jgraichen/railway-signals/kicad/Hauptsignal/README.md

# Hauptsignal HSv1

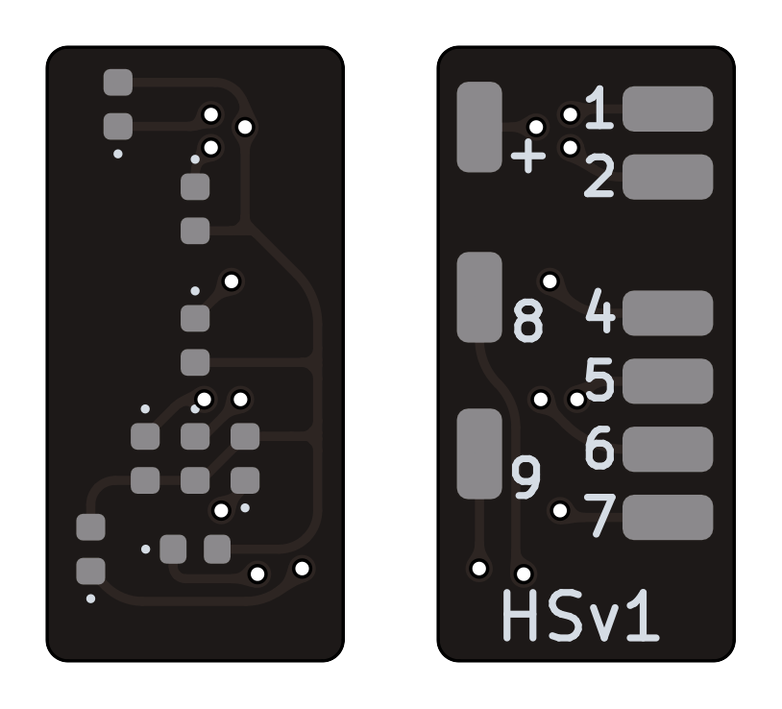
[picture p16: kicad/Hauptsignal/Hauptsignal.png]


Geeignet für KS-Hauptsignale.

## Anschlussbelegung

| Schema | Pin-Belegung |
| --- | --- |
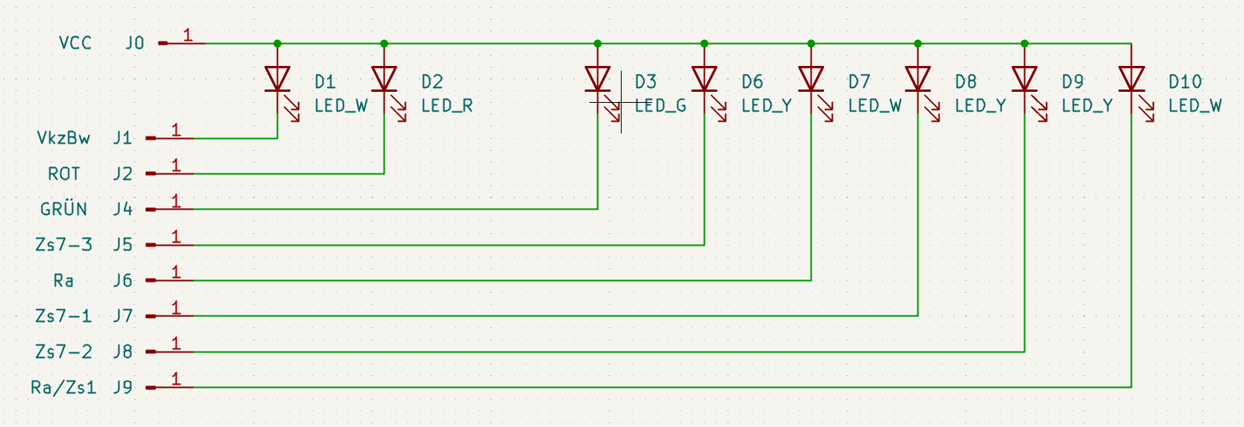
[picture p17: kicad/Hauptsignal/schema.png]
Schema
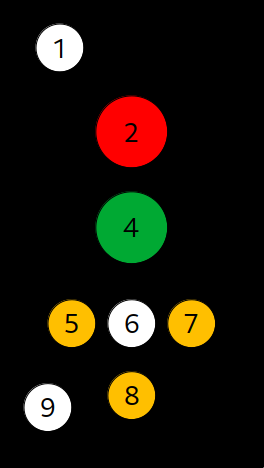
[picture p18: kicad/Hauptsignal/schema_vis.png]
Pin-Belegung
|  |  |

| Referenz | Pin | LED | Funktion |
| --- | --- | --- | --- |
| J0 | + | | Stromversorgung (+) |
| J1 | 1 | Kaltweiß | Zusatzlicht (oben) |
| J2 | 2 | Rot | Hp0 (Halt) |
| J4 | 4 | Grün | Ks1 (Fahrt) |
| J5 | 5 | Gelb | Zs7 |
| J6 | 6 | Kaltweiß | Sh1/Ra12 |
| J7 | 7 | Gelb | Zs7 |
| J8 | 8 | Gelb | Zs7 |
| J9 | 9 | Kaltweiß | Sh1/Ra12/Zs1/Zusatzlicht (unten) |

## License

This work is licensed under a
[Creative Commons Attribution-ShareAlike 4.0 International License](http://creativecommons.org/licenses/by-sa/4.0/).

(http://creativecommons.org/licenses/by-sa/4.0/)
