jgraichen/railway-signals/freecad/KS/Example/export/MS_48_80_1-front.png

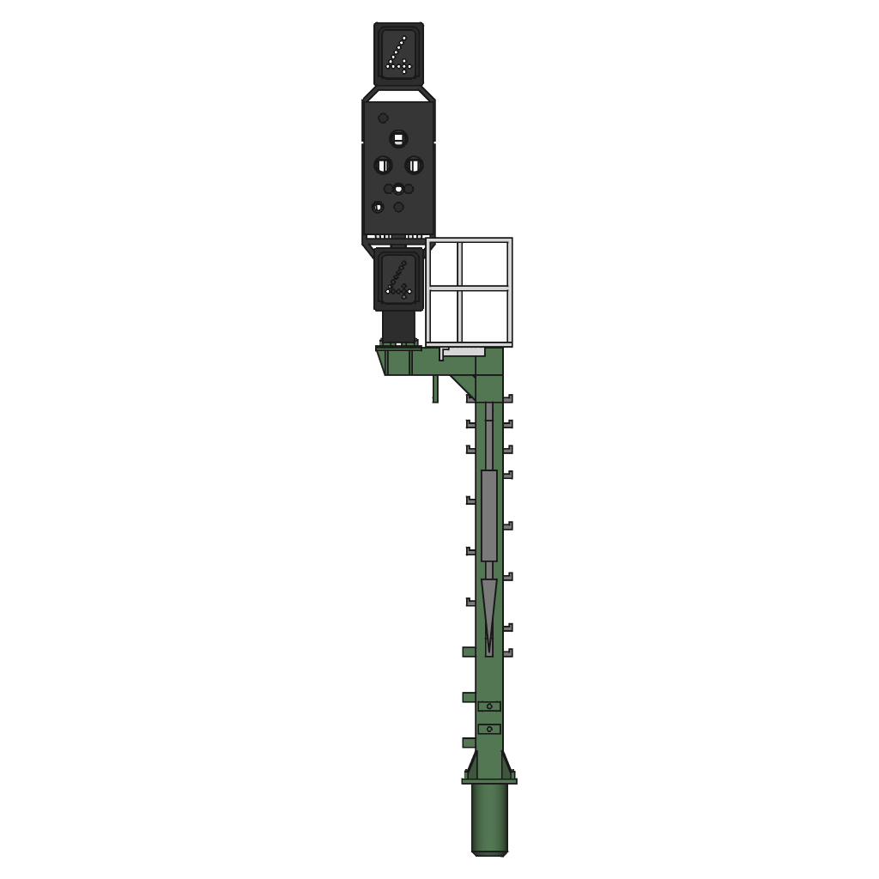
freecad/KS/Example/export/MS_48_80_1-front.png
