jgraichen/railway-signals/freecad/KS/Signalschirme/export/MS__B-axo.png

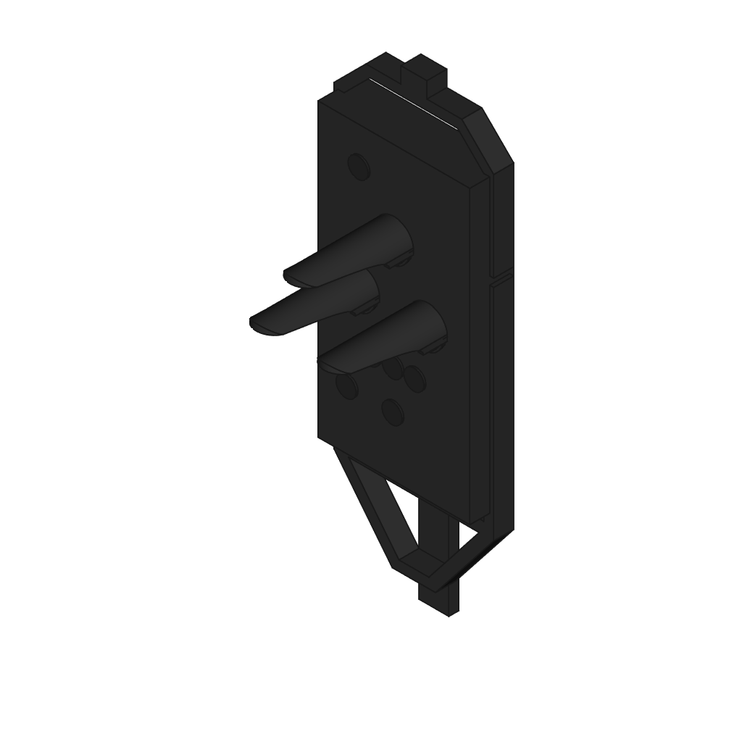
freecad/KS/Signalschirme/export/MS__B-axo.png
