jgraichen/railway-signals/freecad/KS/Zusatzsignale/export/ZS_Zs2_P-axo.png

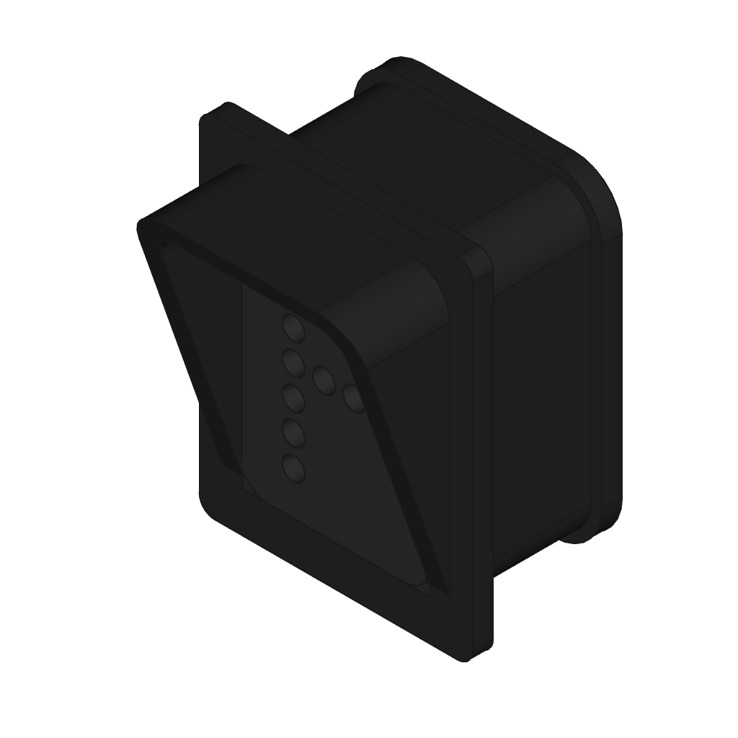
freecad/KS/Zusatzsignale/export/ZS_Zs2_P-axo.png
