jgraichen/railway-signals/freecad/KS/Zusatzsignale/export/ZS_Zs6_NR-axo.png

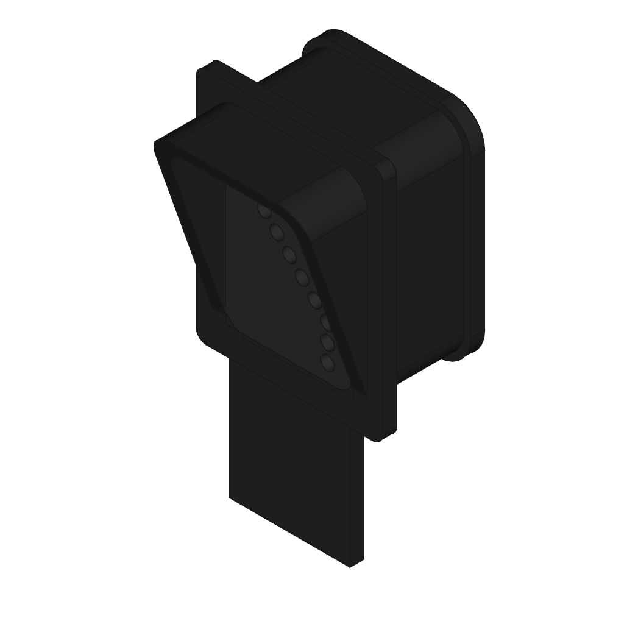
freecad/KS/Zusatzsignale/export/ZS_Zs6_NR-axo.png
