jgraichen/railway-signals/freecad/watti-signal-mount/png/watti-plate-axo.png

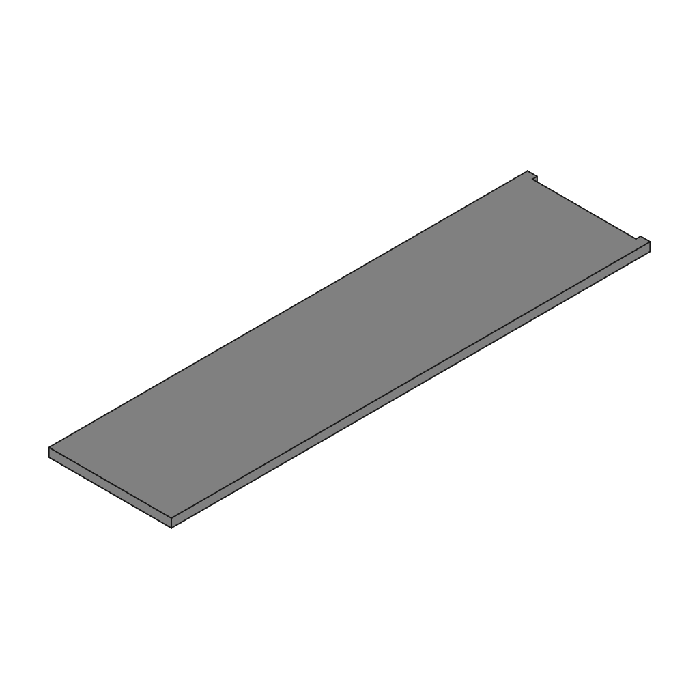
freecad/watti-signal-mount/png/watti-plate-axo.png
