jgraichen/railway-signals/freecad/KS/Signalschirme/export/MS_Zs7_Sh1_vBw__B.step

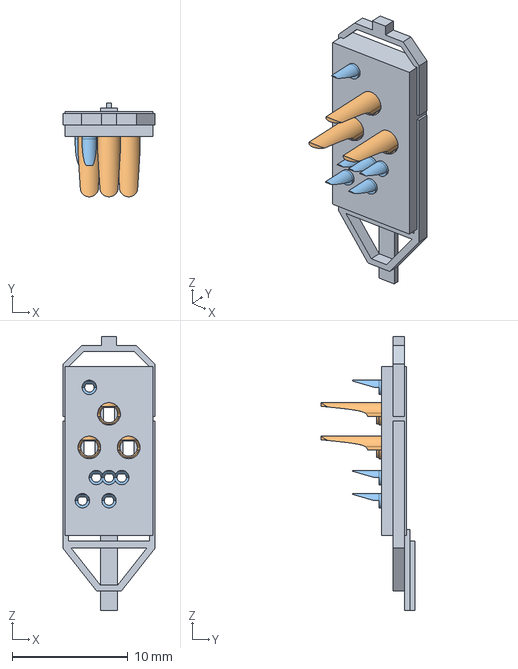
[picture p129: CAD file, 2026-01-25]
freecad/KS/Signalschirme/export/MS_Zs7_Sh1_vBw__B.step
8.00 x 8.10 x 23.7 mm
