jgraichen/railway-signals/freecad/KS/Signalschirme/parts/HS_Schute_15.FCStd

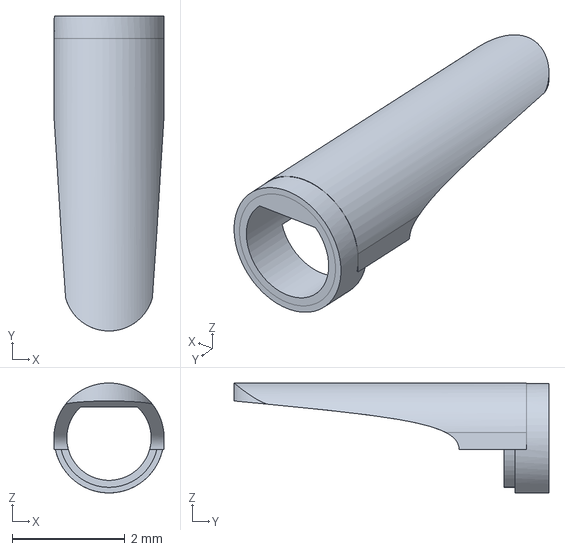
[picture p130: CAD file, 2026-01-25]
freecad/KS/Signalschirme/parts/HS_Schute_15.FCStd
1.95 x 5.60 x 1.96 mm
