jgraichen/railway-signals/freecad/KS/Zusatzsignale/export/ZS_Zs3_3.step

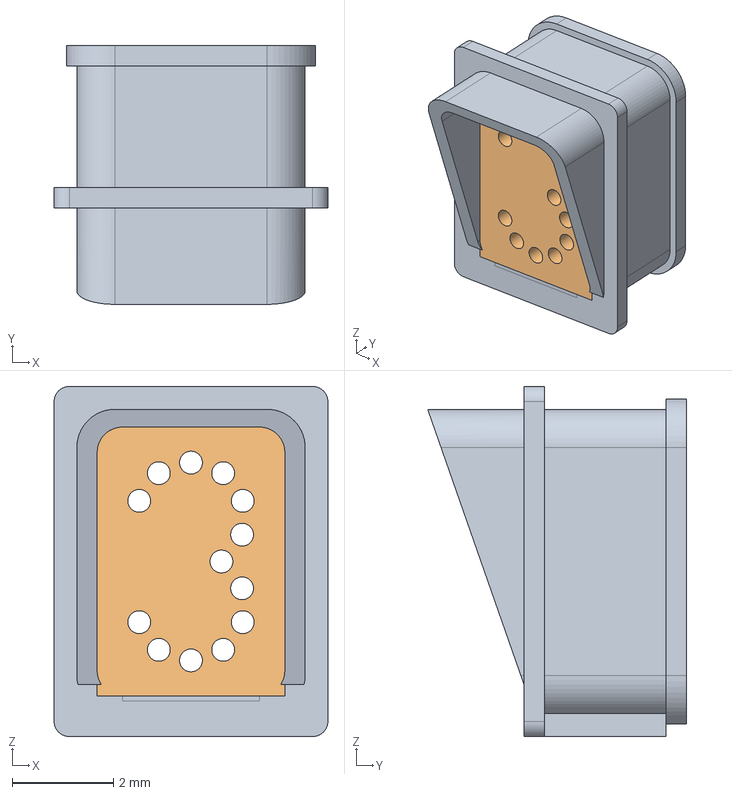
[picture p131: CAD file, 2026-01-25]
freecad/KS/Zusatzsignale/export/ZS_Zs3_3.step
5.40 x 5.10 x 6.90 mm
