jgraichen/railway-signals/freecad/watti-signal-mount/export/watti-plate.step

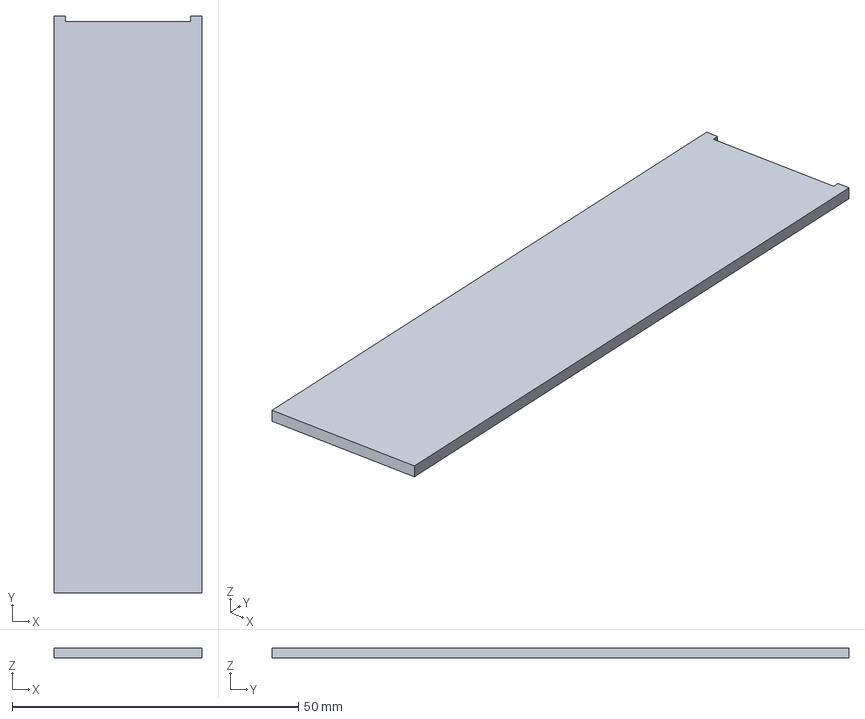
[picture p132: CAD file, 2024-03-24]
freecad/watti-signal-mount/export/watti-plate.step
25.8 x 100.8 x 1.80 mm
