jgraichen/railway-signals/freecad/watti-signal-mount/parts/M3-mount.FCStd

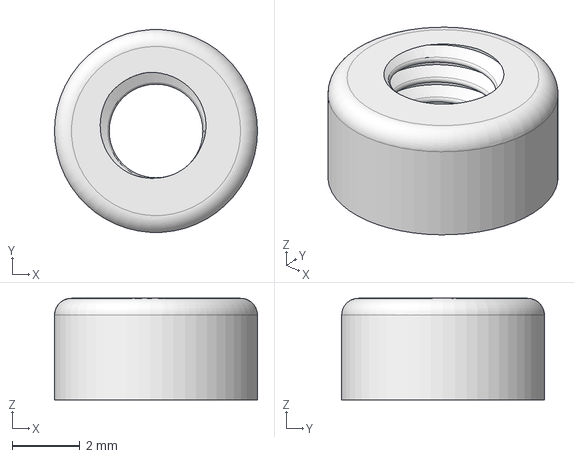
[picture p133: CAD file, 2023-12-09]
freecad/watti-signal-mount/parts/M3-mount.FCStd
6.00 x 5.99 x 3.00 mm
