jgraichen/railway-signals/freecad/KS/Masten/export/Auslegermast_48_40L_1ZS.step

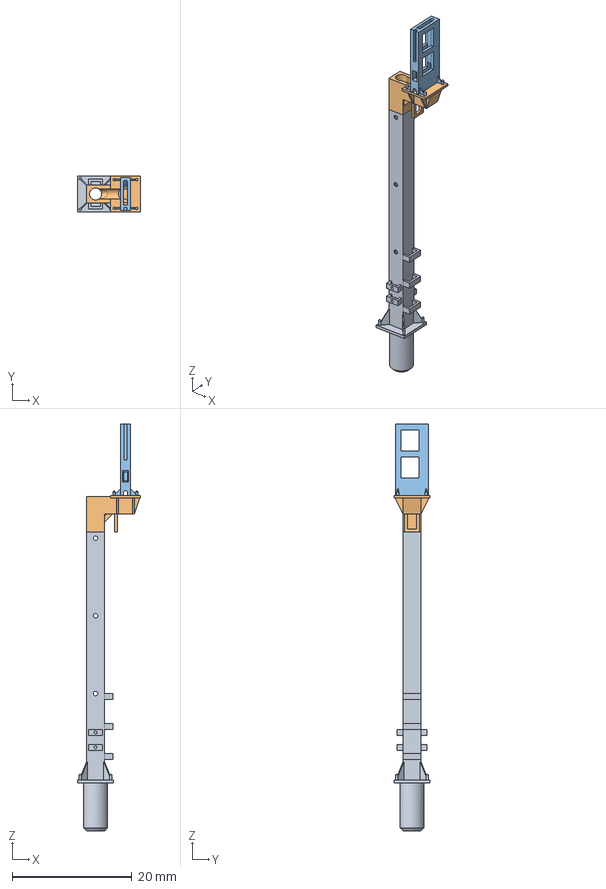
[picture p134: CAD file, 2024-05-25]
freecad/KS/Masten/export/Auslegermast_48_40L_1ZS.step
10.5 x 6.00 x 68.1 mm
Mast_42
Ausleger_40
Signalmast_1ZS
