jgraichen/railway-signals/freecad/KS/Masten/parts/Part_Mast_42.FCStd

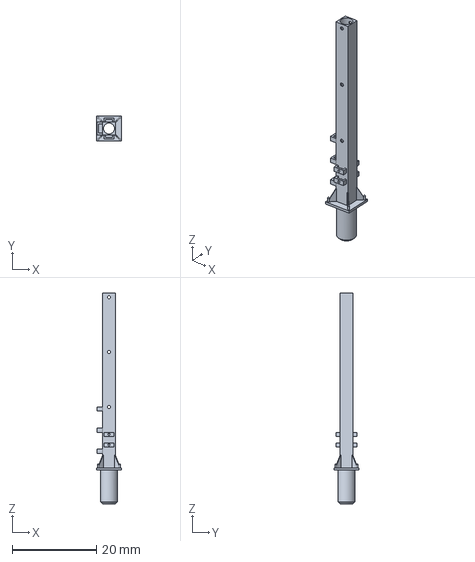
[picture p135: CAD file, 2024-06-06]
freecad/KS/Masten/parts/Part_Mast_42.FCStd
6.00 x 6.00 x 50.0 mm
