jgraichen/railway-signals/freecad/KS/Signalschirme/parts/MS_Schirm_mit_Zs.FCStd

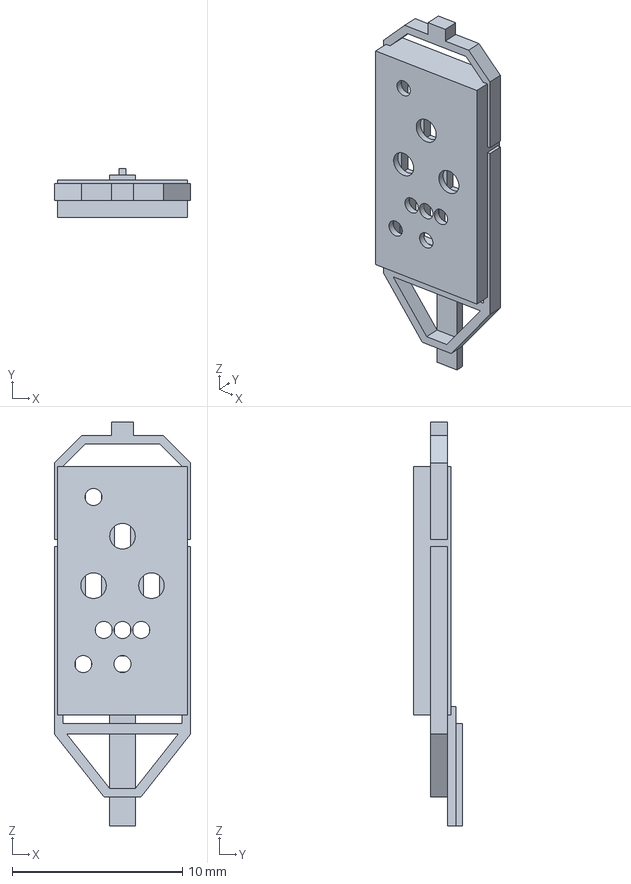
[picture p137: CAD file, 2026-01-25]
freecad/KS/Signalschirme/parts/MS_Schirm_mit_Zs.FCStd
8.00 x 2.90 x 23.7 mm
