jgraichen/railway-signals/freecad/KS/Zusatzsignale/parts/ZS_Nummer.FCStd

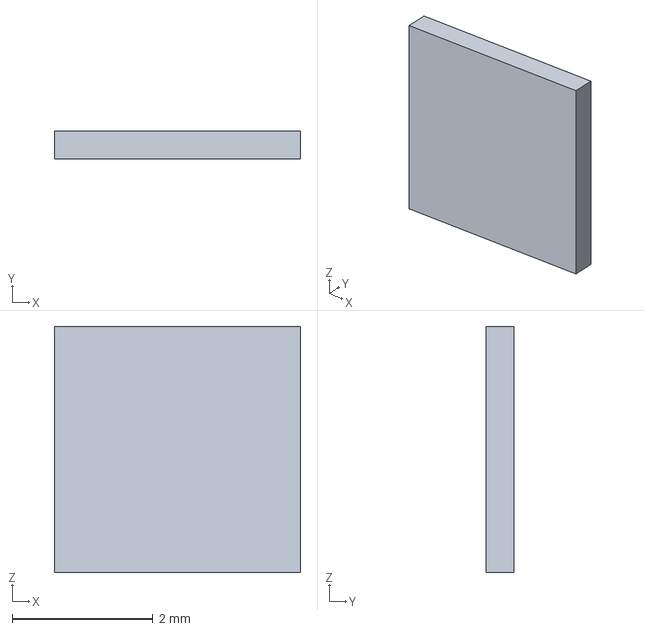
[picture p138: CAD file, 2026-01-25]
freecad/KS/Zusatzsignale/parts/ZS_Nummer.FCStd
3.50 x 0.4 x 3.50 mm
