jgraichen/railway-signals/freecad/KS/Masten/export/Leiter_16.step

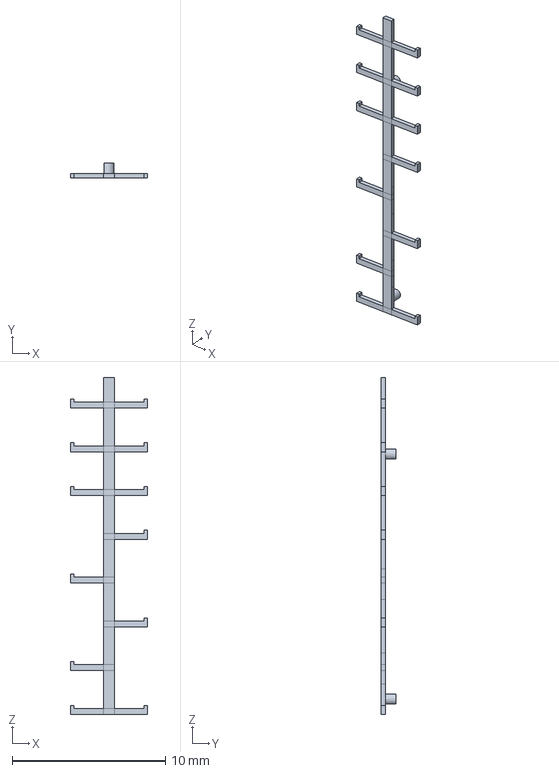
[picture p139: CAD file, 2024-05-24]
freecad/KS/Masten/export/Leiter_16.step
5.00 x 1.00 x 22.0 mm
