jgraichen/railway-signals/freecad/KS/Masten/parts/Part_Mast_52.FCStd

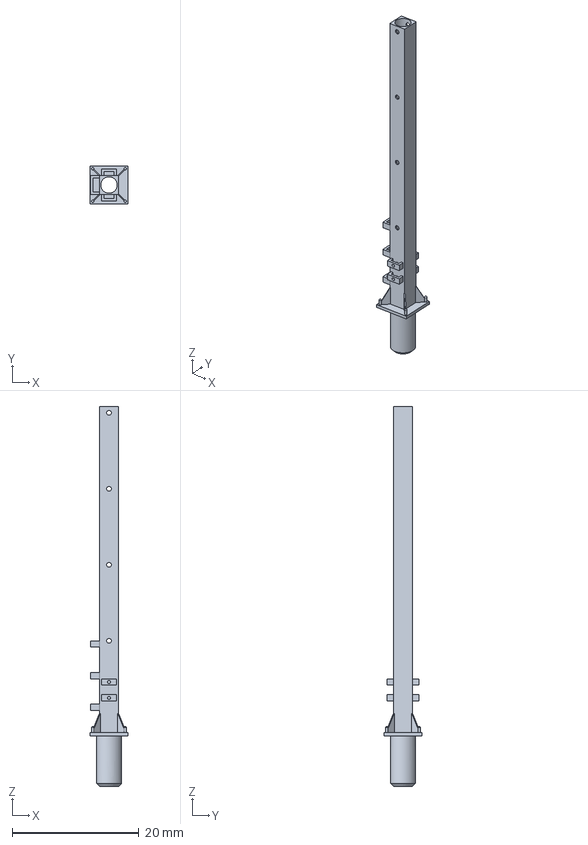
[picture p140: CAD file, 2024-05-24]
freecad/KS/Masten/parts/Part_Mast_52.FCStd
6.00 x 6.00 x 60.0 mm
