jgraichen/railway-signals/freecad/KS/Signalschirme/parts/HS_Schirm_Blindstopfen_10.FCStd

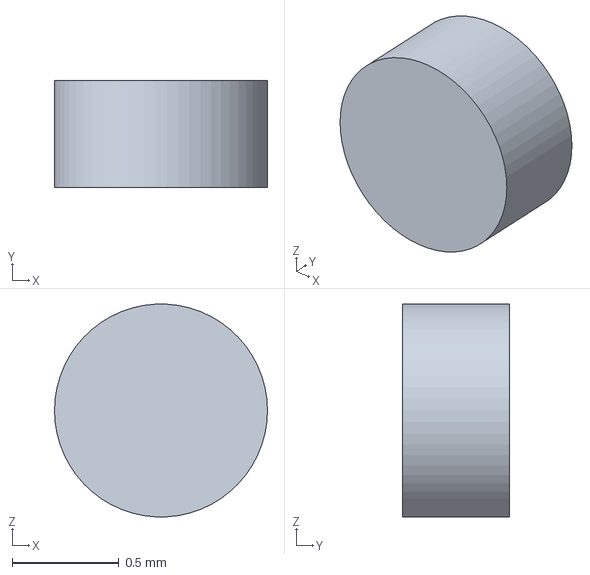
[picture p142: CAD file, 2026-01-25]
freecad/KS/Signalschirme/parts/HS_Schirm_Blindstopfen_10.FCStd
1.00 x 0.5 x 0.999 mm
