jgraichen/railway-signals/freecad/KS/Zusatzsignale/parts/ZS_Tafel_2.FCStd

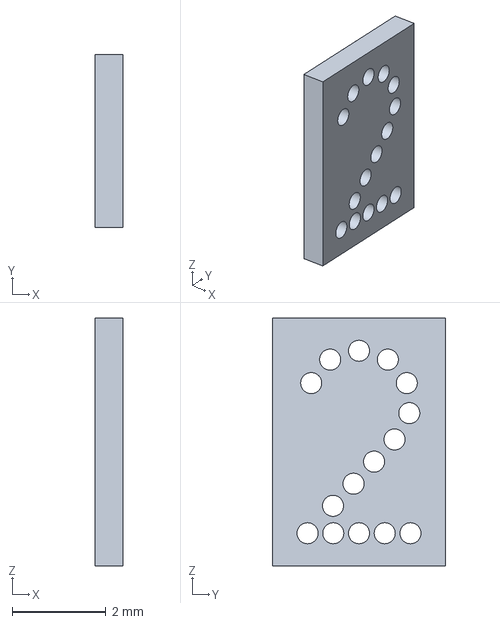
[picture p143: CAD file, 2026-01-25]
freecad/KS/Zusatzsignale/parts/ZS_Tafel_2.FCStd
0.6 x 3.70 x 5.30 mm
