jgraichen/railway-signals/freecad/KS/Masten/export/Auslegermast_48_40R_1ZS.step

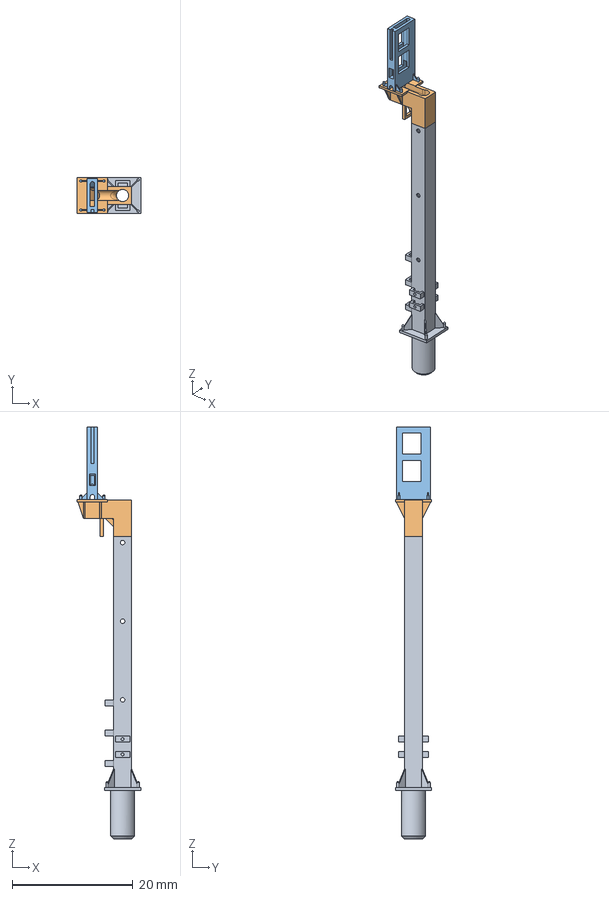
[picture p144: CAD file, 2024-05-24]
freecad/KS/Masten/export/Auslegermast_48_40R_1ZS.step
10.5 x 6.00 x 68.1 mm
Mast_42
Ausleger_40
Signalmast_1ZS
