jgraichen/railway-signals/freecad/KS/Masten/parts/Part_Ausleger_80.FCStd

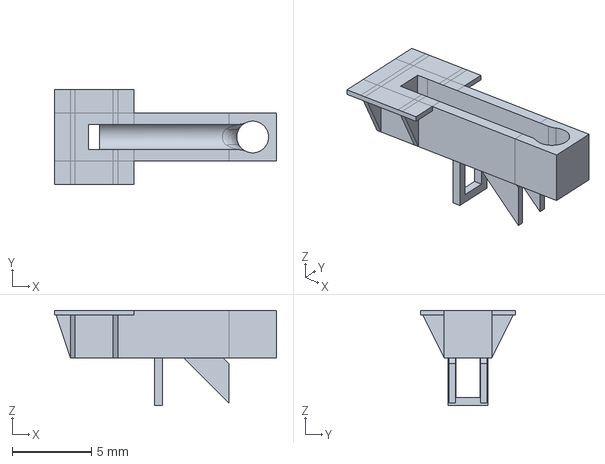
[picture p145: CAD file, 2024-05-24]
freecad/KS/Masten/parts/Part_Ausleger_80.FCStd
14.0 x 6.00 x 6.00 mm
