jgraichen/railway-signals/freecad/KS/Signalschirme/export/VS_Wd.step

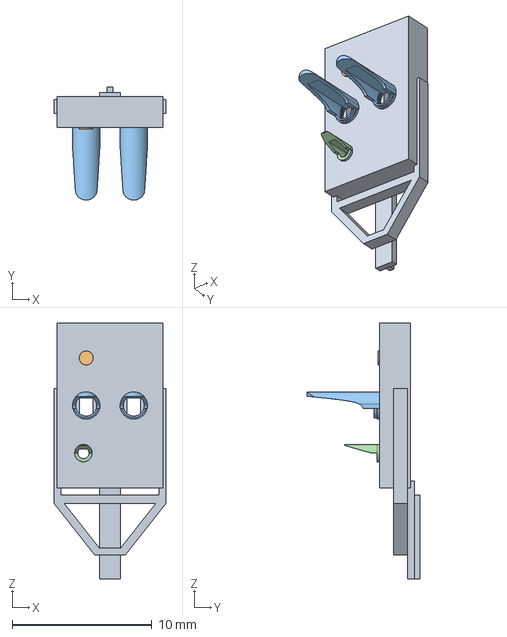
[picture p146: CAD file, 2024-03-24]
freecad/KS/Signalschirme/export/VS_Wd.step
8.00 x 8.10 x 18.3 mm
