jgraichen/railway-signals/freecad/KS/Masten/export/Mast_Korb_1.step

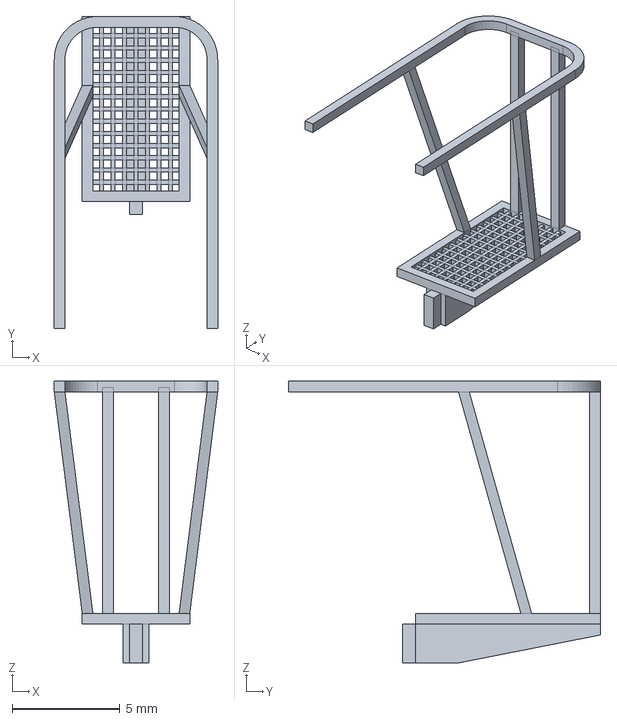
[picture p148: CAD file, 2024-05-24]
freecad/KS/Masten/export/Mast_Korb_1.step
7.60 x 14.5 x 13.1 mm
