jgraichen/railway-signals/freecad/KS/Masten/parts/Part_Signalmast_2ZS.FCStd

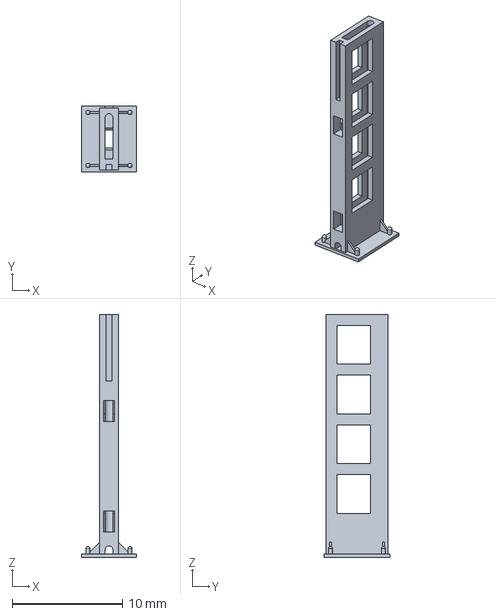
[picture p149: CAD file, 2024-05-24]
freecad/KS/Masten/parts/Part_Signalmast_2ZS.FCStd
5.00 x 6.00 x 22.0 mm
