jgraichen/railway-signals/freecad/KS/Signalschirme/parts/VS_Schirm.FCStd

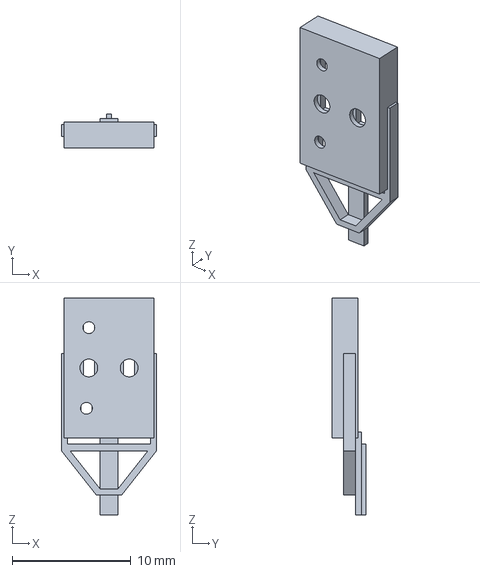
[picture p151: CAD file, 2024-01-25]
freecad/KS/Signalschirme/parts/VS_Schirm.FCStd
8.00 x 2.90 x 18.3 mm
