jgraichen/railway-signals/freecad/KS/Zusatzsignale/parts/ZS_Signal.FCStd

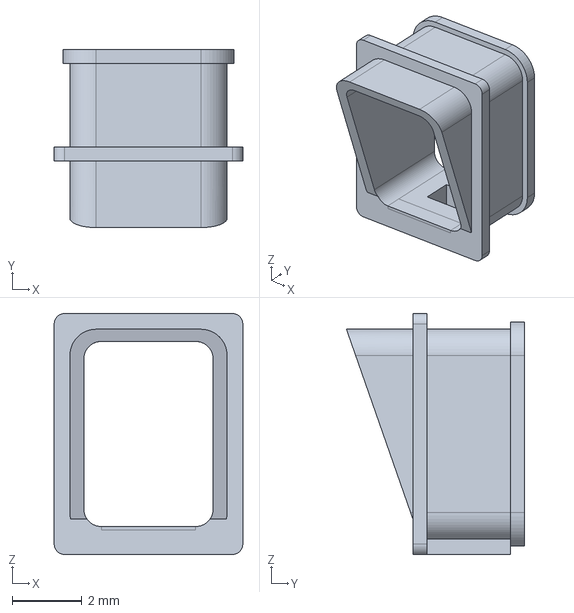
[picture p152: CAD file, 2026-01-25]
freecad/KS/Zusatzsignale/parts/ZS_Signal.FCStd
5.40 x 5.10 x 6.90 mm
