jgraichen/railway-signals/freecad/KS/Masten/export/Technik_1.step

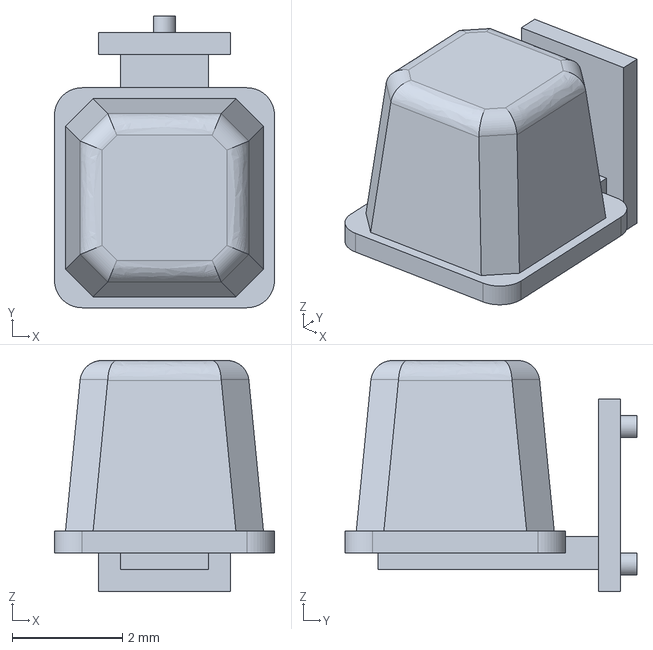
[picture p153: CAD file, 2024-05-24]
freecad/KS/Masten/export/Technik_1.step
4.00 x 5.30 x 4.20 mm
