jgraichen/railway-signals/freecad/KS/Masten/parts/Part_Mast_32.FCStd

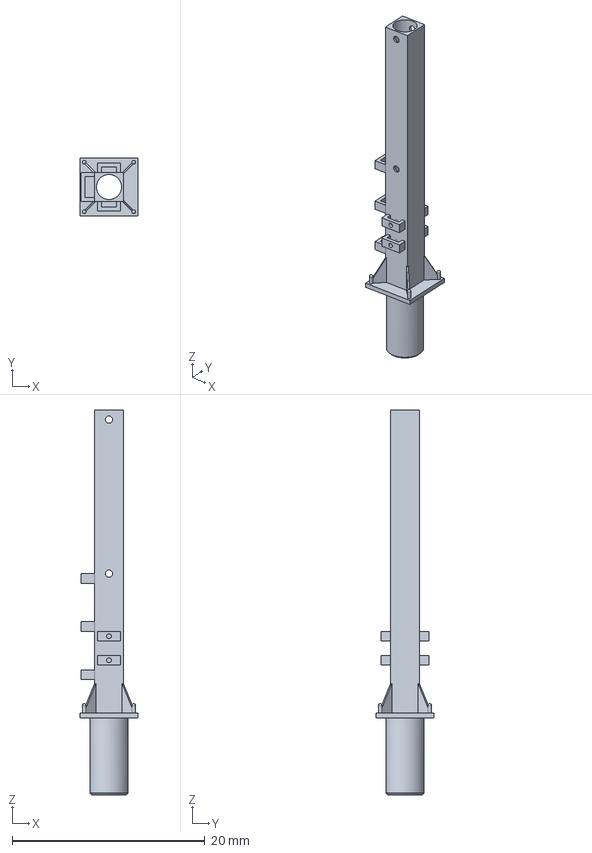
[picture p154: CAD file, 2024-05-24]
freecad/KS/Masten/parts/Part_Mast_32.FCStd
6.00 x 6.00 x 40.0 mm
