jgraichen/railway-signals/freecad/KS/Signalschirme/export/VS.step

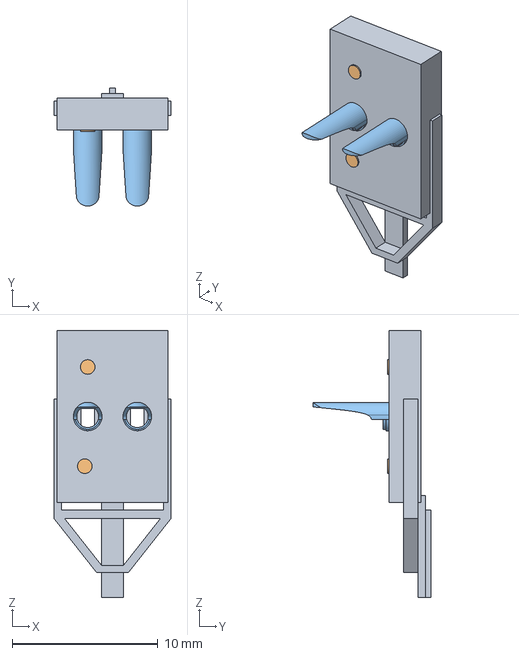
[picture p155: CAD file, 2024-03-24]
freecad/KS/Signalschirme/export/VS.step
8.00 x 8.10 x 18.3 mm
