jgraichen/railway-signals/freecad/KS/Signalschirme/parts/HS_Schirm_ohne_Zs.FCStd

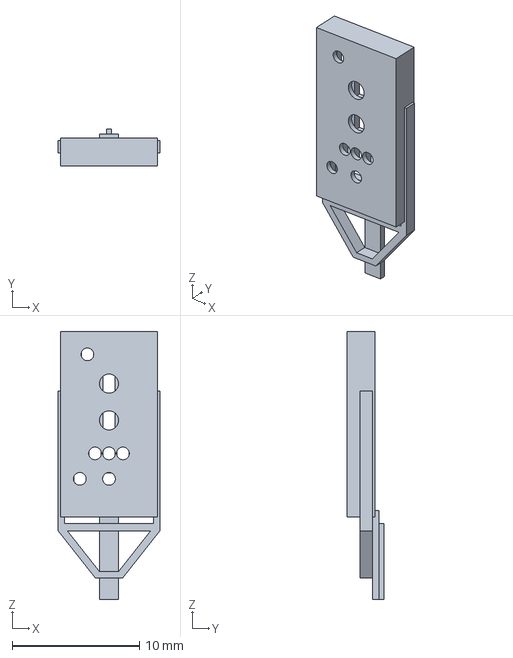
[picture p156: CAD file, 2024-01-25]
freecad/KS/Signalschirme/parts/HS_Schirm_ohne_Zs.FCStd
8.00 x 2.90 x 21.1 mm
