jgraichen/railway-signals/freecad/KS/Zusatzsignale/export/ZS_Halterung.step

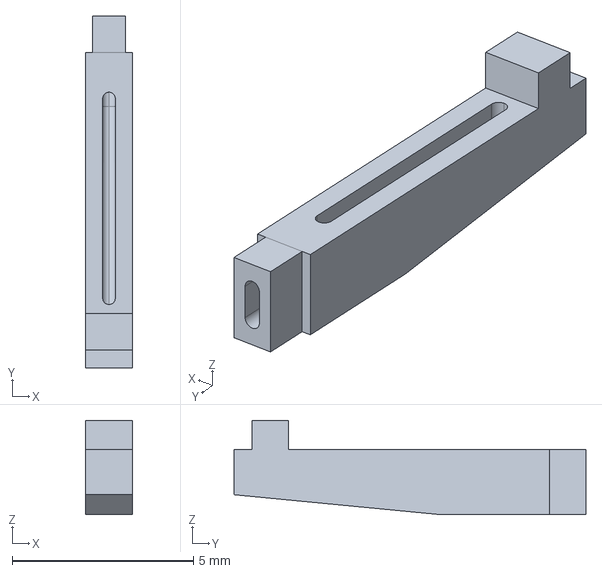
[picture p157: CAD file, 2024-03-24]
freecad/KS/Zusatzsignale/export/ZS_Halterung.step
1.30 x 9.70 x 2.60 mm
