jgraichen/railway-signals/freecad/KS/Zusatzsignale/parts/ZS_Tafel_Zs6_GG.FCStd

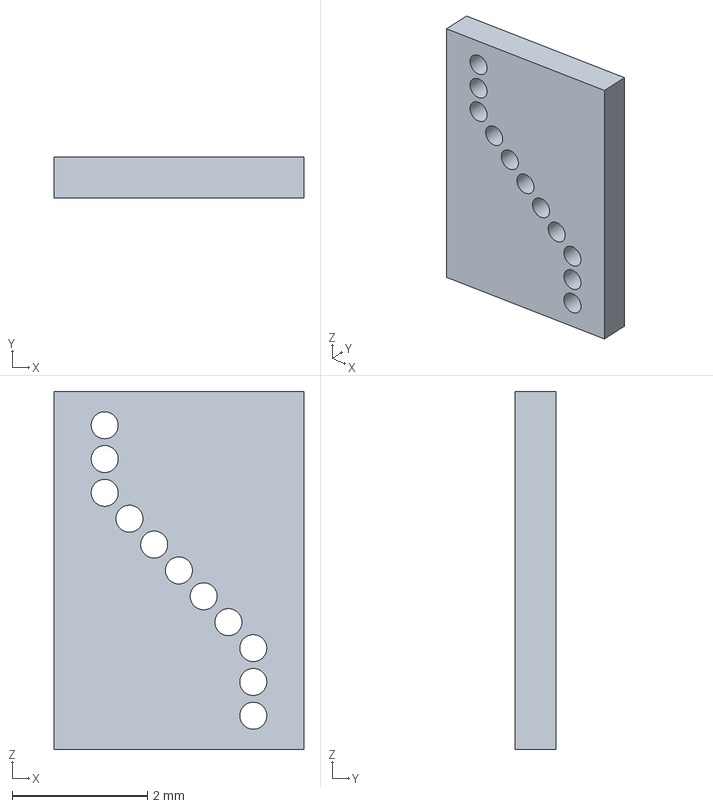
[picture p158: CAD file, 2024-01-25]
freecad/KS/Zusatzsignale/parts/ZS_Tafel_Zs6_GG.FCStd
3.70 x 0.6 x 5.30 mm
