jgraichen/railway-signals/freecad/KS/Masten/export/Mastschild_16_VS.step

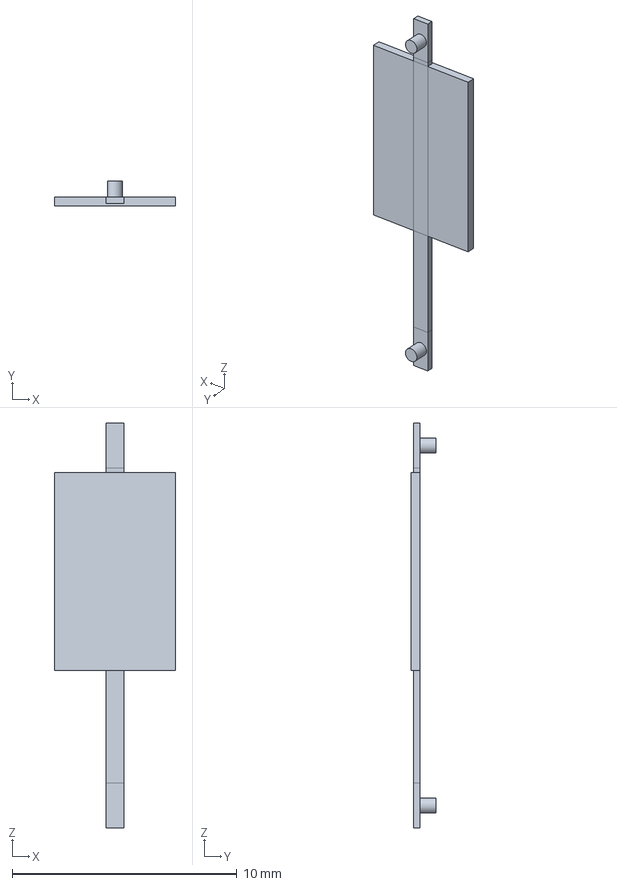
[picture p159: CAD file, 2024-05-24]
freecad/KS/Masten/export/Mastschild_16_VS.step
5.40 x 1.10 x 18.0 mm
