jgraichen/railway-signals/freecad/KS/Signalschirme/export/MS_Zs7_vBw__A.step

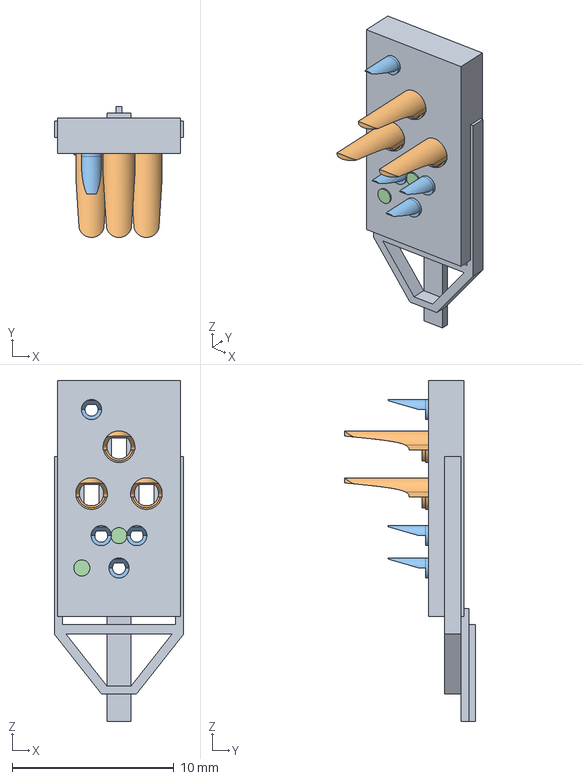
[picture p160: CAD file, 2024-03-24]
freecad/KS/Signalschirme/export/MS_Zs7_vBw__A.step
8.00 x 8.10 x 21.1 mm
