jgraichen/railway-signals/freecad/KS/Zusatzsignale/export/ZS_Diffusor_48um.step

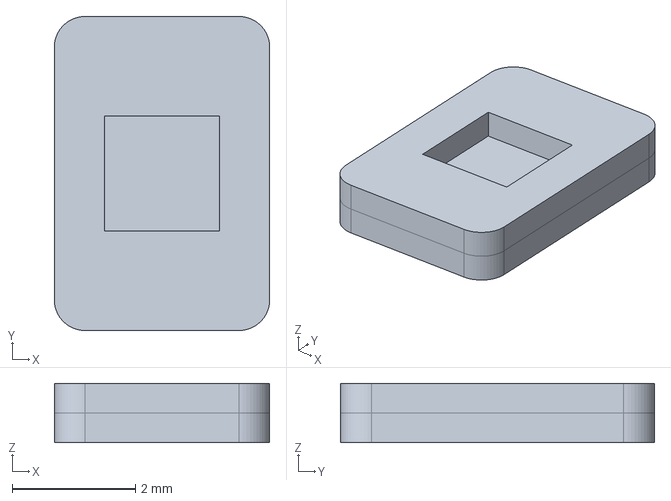
[picture p161: CAD file, 2024-03-24]
freecad/KS/Zusatzsignale/export/ZS_Diffusor_48um.step
3.50 x 5.10 x 0.96 mm
