jgraichen/railway-signals/freecad/KS/Masten/export/Mastschild_26_VS.step

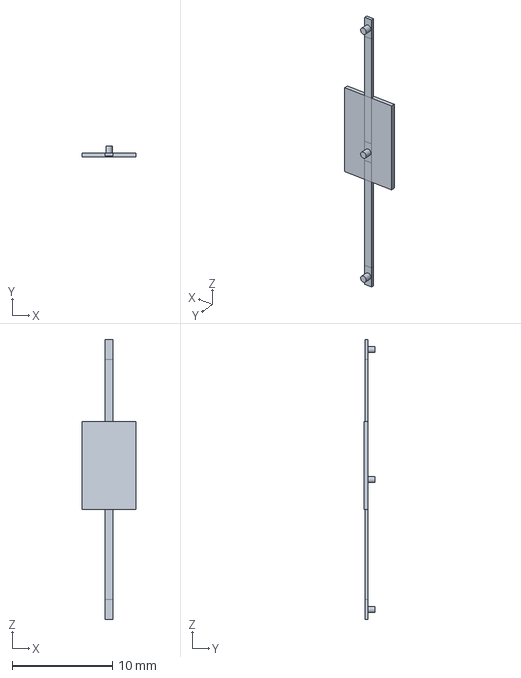
[picture p162: CAD file, 2024-05-24]
freecad/KS/Masten/export/Mastschild_26_VS.step
5.40 x 1.10 x 28.0 mm
