jgraichen/railway-signals/freecad/KS/Signalschirme/parts/HS_Schirm_Blindstopfen_15.FCStd

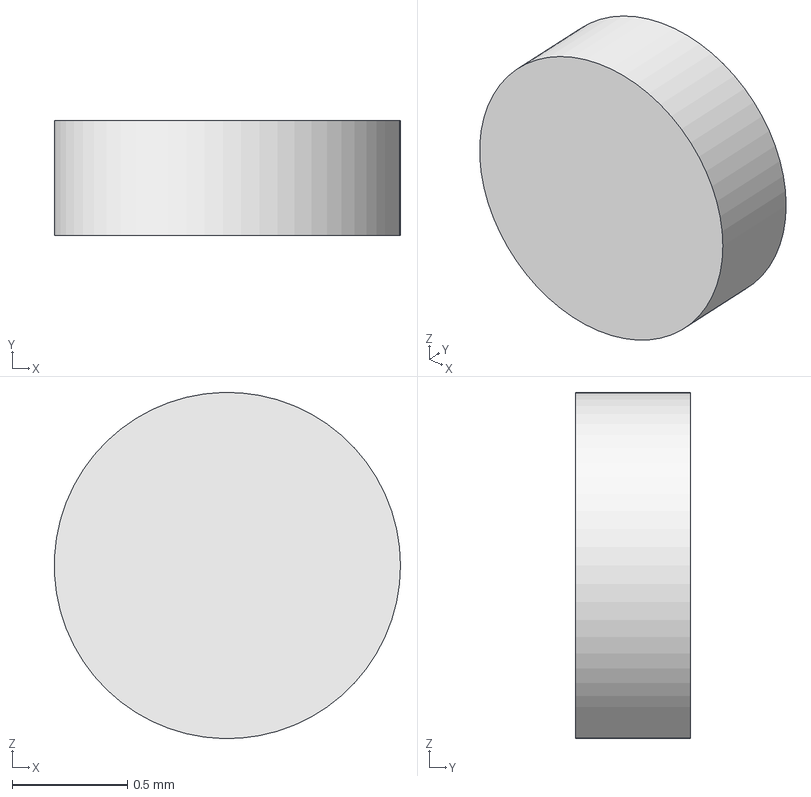
[picture p163: CAD file, 2024-01-25]
freecad/KS/Signalschirme/parts/HS_Schirm_Blindstopfen_15.FCStd
1.50 x 0.5 x 1.50 mm
