jgraichen/railway-signals/freecad/KS/Zusatzsignale/export/ZS_Diffusor_96um.step

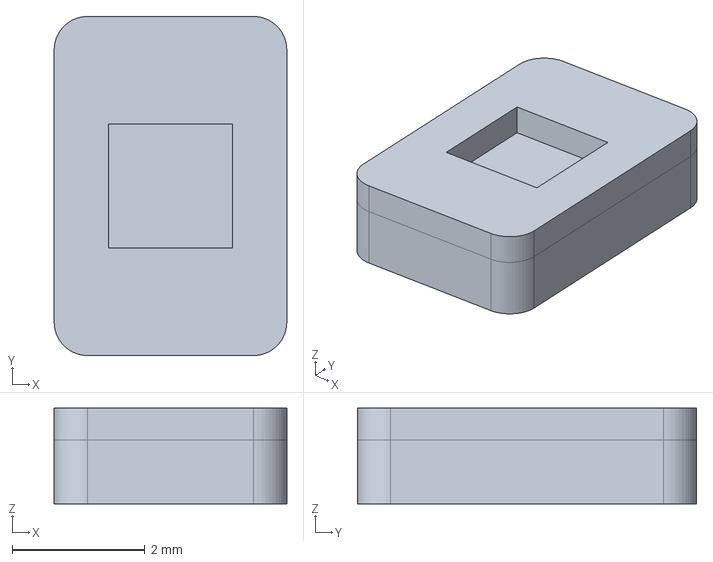
[picture p164: CAD file, 2024-03-24]
freecad/KS/Zusatzsignale/export/ZS_Diffusor_96um.step
3.50 x 5.10 x 1.44 mm
