jgraichen/railway-signals/freecad/KS/Masten/export/Mastschild_16_MS.step

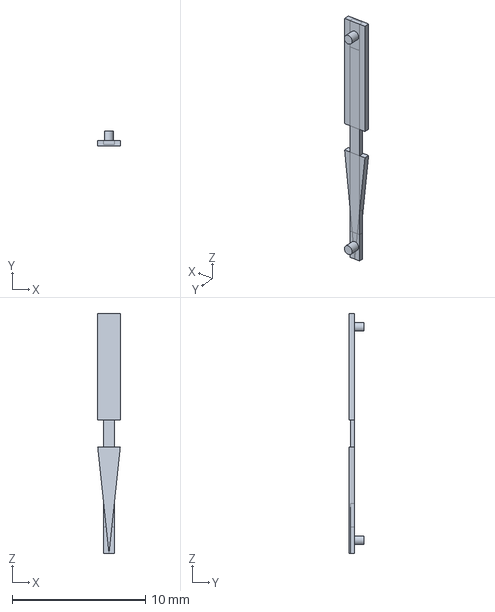
[picture p165: CAD file, 2024-05-24]
freecad/KS/Masten/export/Mastschild_16_MS.step
1.70 x 1.10 x 18.0 mm
