jgraichen/railway-signals/freecad/KS/Signalschirme/export/MS__B.step

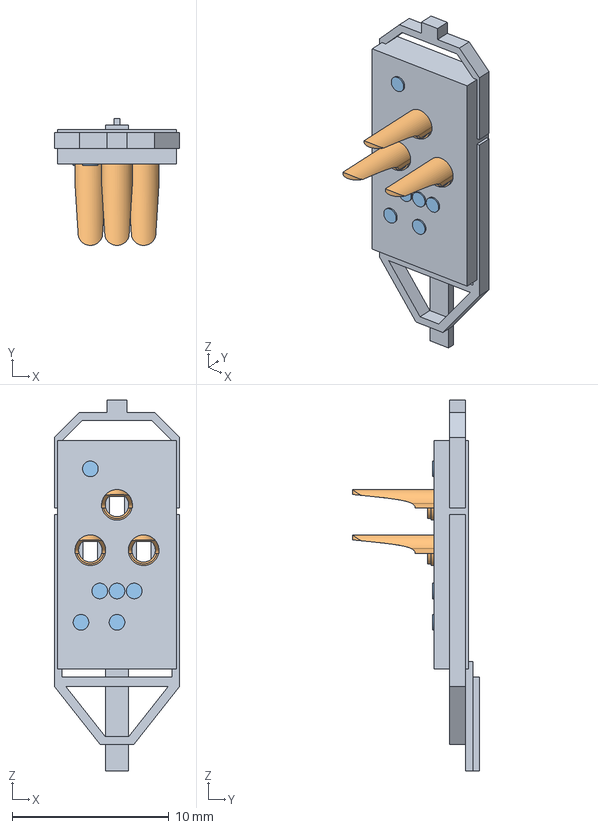
[picture p166: CAD file, 2024-03-24]
freecad/KS/Signalschirme/export/MS__B.step
8.00 x 8.10 x 23.7 mm
