jgraichen/railway-signals/freecad/KS/Zusatzsignale/export/ZS_Zs6_NR.step

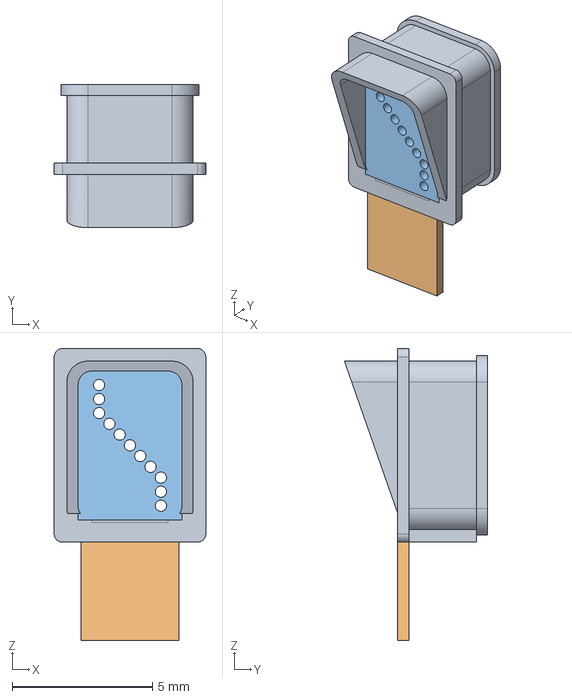
[picture p167: CAD file, 2024-03-24]
freecad/KS/Zusatzsignale/export/ZS_Zs6_NR.step
5.40 x 5.10 x 10.4 mm
