jgraichen/railway-signals/freecad/KS/Masten/export/Leiter_16_0504.step

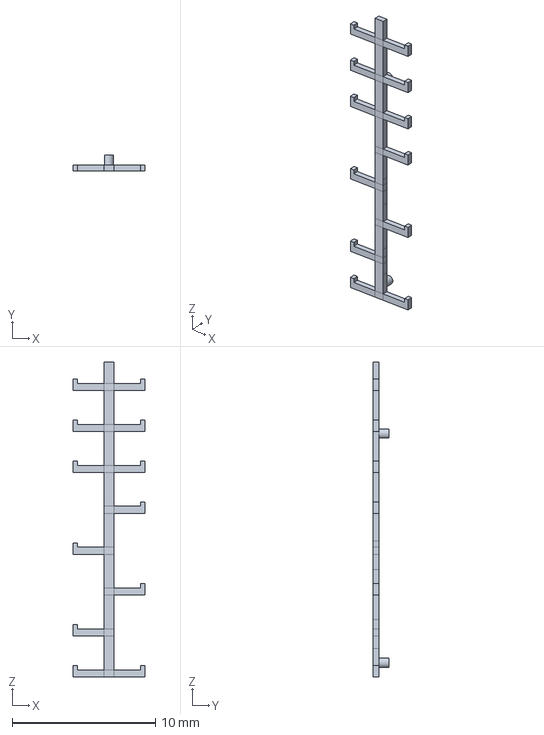
[picture p168: CAD file, 2024-05-24]
freecad/KS/Masten/export/Leiter_16_0504.step
5.00 x 1.10 x 22.0 mm
