jgraichen/railway-signals/freecad/KS/Signalschirme/export/MS_Sh1_vBw__A.step

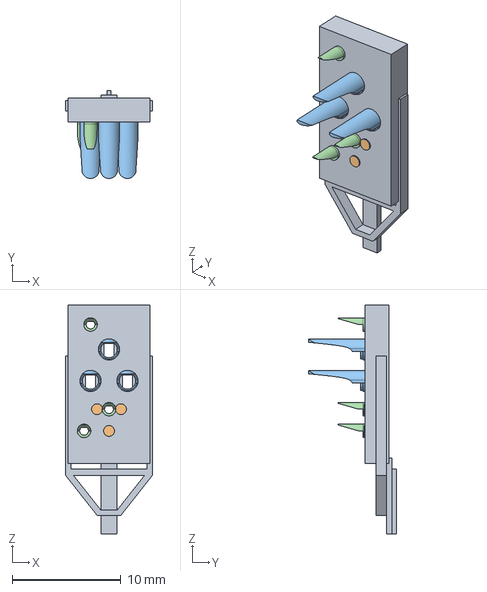
[picture p169: CAD file, 2024-03-24]
freecad/KS/Signalschirme/export/MS_Sh1_vBw__A.step
8.00 x 8.10 x 21.1 mm
