jgraichen/railway-signals/freecad/KS/Zusatzsignale/export/ZS_Zs3v_Fest.step

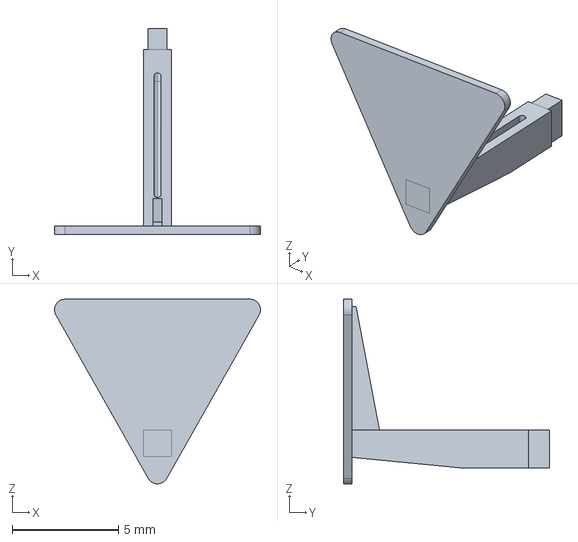
[picture p170: CAD file, 2024-03-24]
freecad/KS/Zusatzsignale/export/ZS_Zs3v_Fest.step
9.69 x 9.70 x 8.68 mm
