jgraichen/railway-signals/freecad/KS/Masten/export/Mastschild_26_MS.step

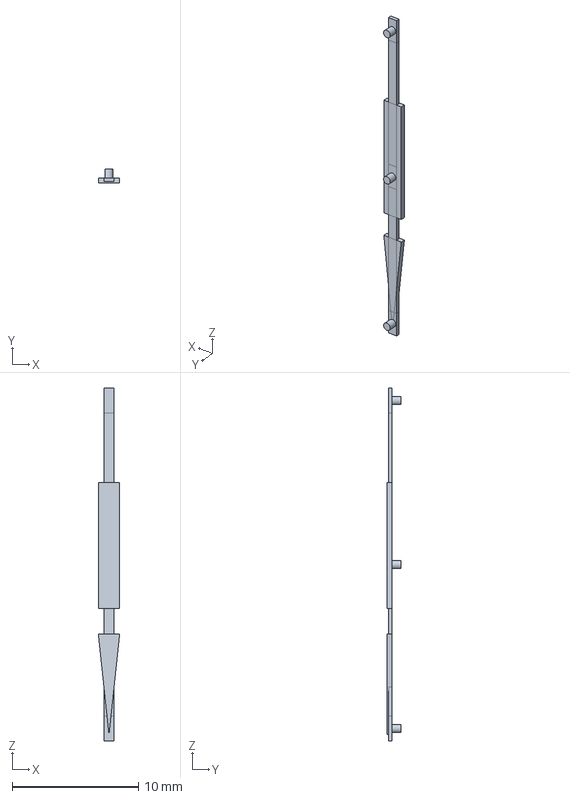
[picture p171: CAD file, 2024-05-24]
freecad/KS/Masten/export/Mastschild_26_MS.step
1.70 x 1.10 x 28.0 mm
