jgraichen/railway-signals/freecad/KS/Masten/export/Leiter_26_0504.step

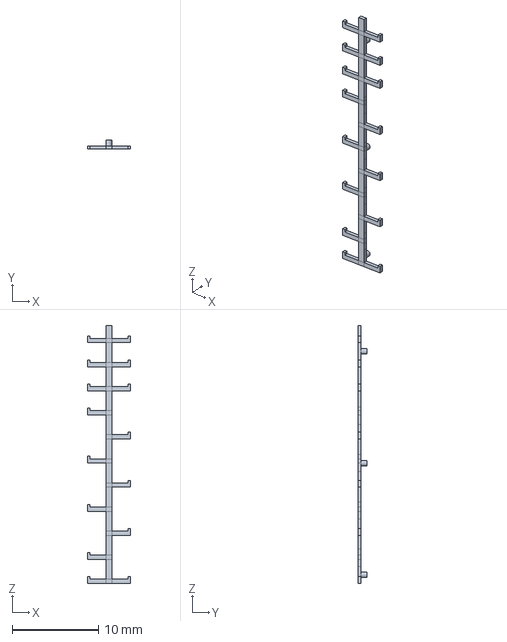
[picture p173: CAD file, 2024-05-24]
freecad/KS/Masten/export/Leiter_26_0504.step
5.00 x 1.10 x 30.0 mm
