jgraichen/railway-signals/freecad/KS/Zusatzsignale/export/ZS_Diffusor_72um.step

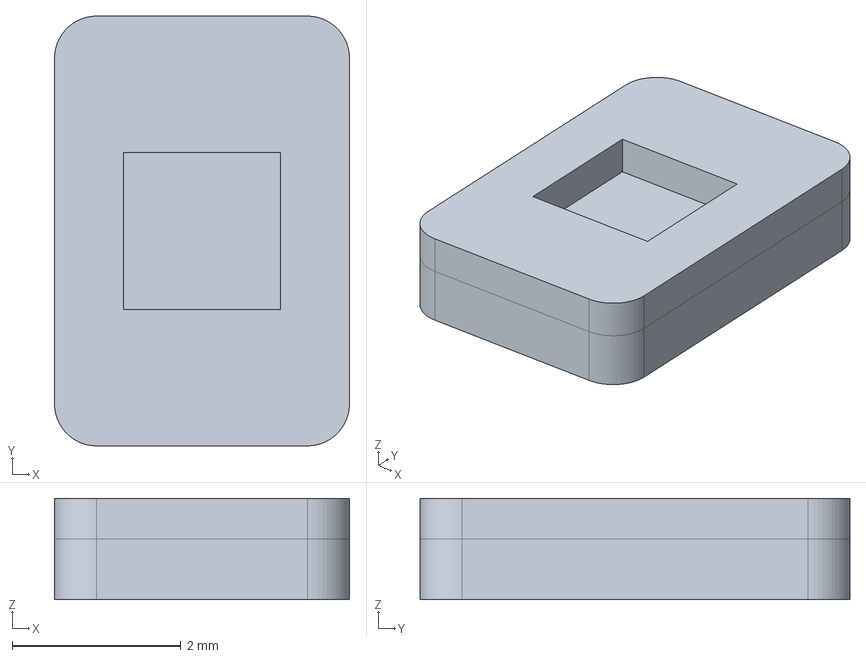
[picture p175: CAD file, 2024-03-24]
freecad/KS/Zusatzsignale/export/ZS_Diffusor_72um.step
3.50 x 5.10 x 1.20 mm
