jgraichen/railway-signals/freecad/KS/Masten/export/Leiter_26.step

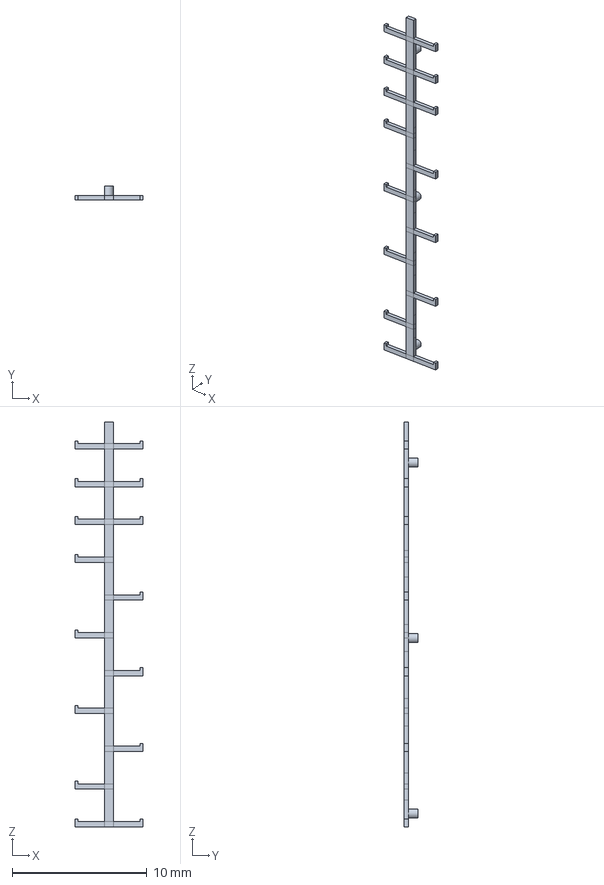
[picture p176: CAD file, 2024-05-24]
freecad/KS/Masten/export/Leiter_26.step
5.00 x 1.00 x 30.0 mm
