jgraichen/railway-signals/freecad/KS/Zusatzsignale/export/ZS_Zs3_Fest.step

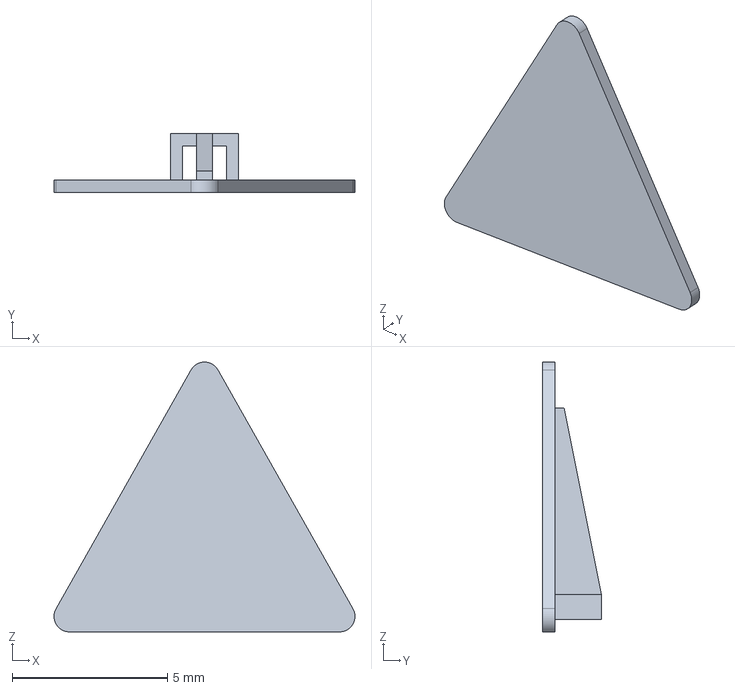
[picture p177: CAD file, 2024-03-24]
freecad/KS/Zusatzsignale/export/ZS_Zs3_Fest.step
9.69 x 1.90 x 8.68 mm
