jgraichen/railway-signals/freecad/KS/Masten/export/Sockel.step

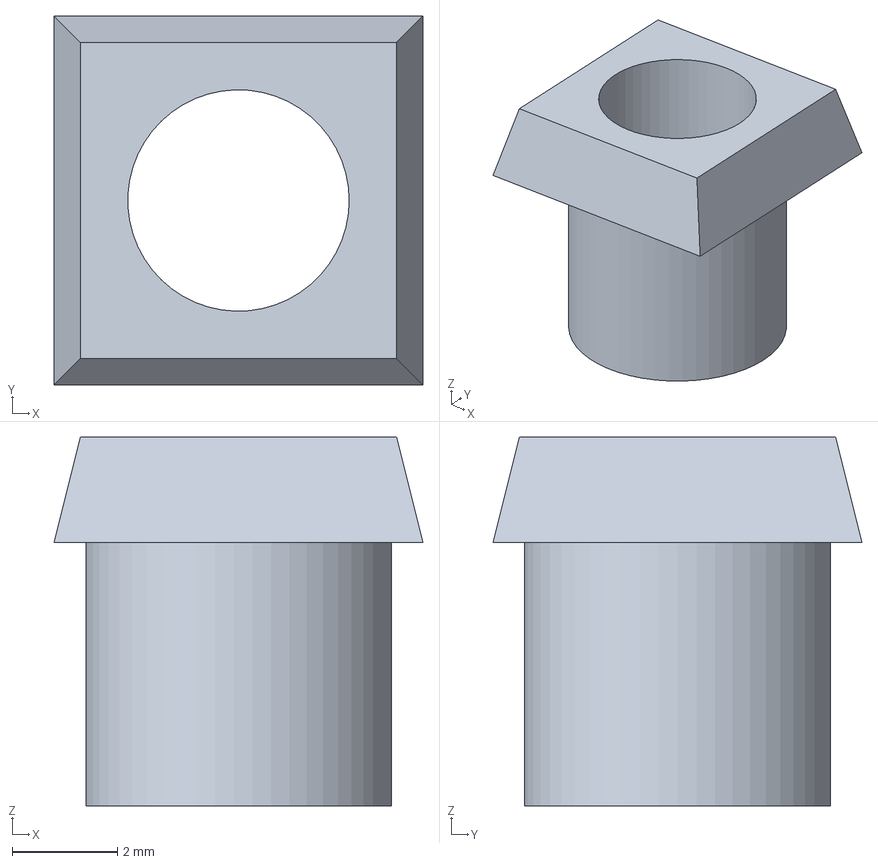
[picture p178: CAD file, 2024-05-24]
freecad/KS/Masten/export/Sockel.step
7.00 x 7.00 x 7.00 mm
