jgraichen/railway-signals/freecad/KS/Signalschirme/export/MS_Sh1__B.step

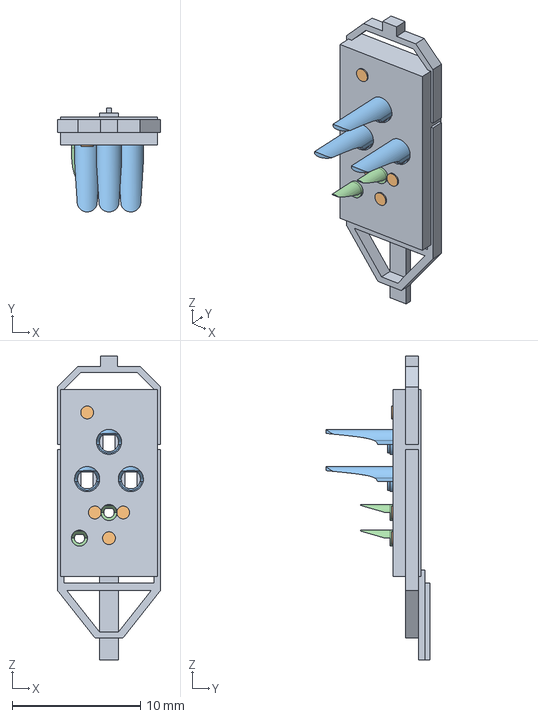
[picture p179: CAD file, 2024-03-24]
freecad/KS/Signalschirme/export/MS_Sh1__B.step
8.00 x 8.10 x 23.7 mm
