jgraichen/railway-signals/freecad/KS/Zusatzsignale/export/ZS_Zs6_Fest_NR.step

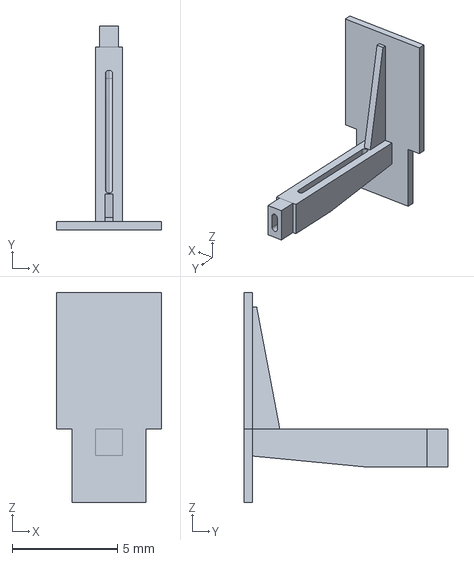
[picture p180: CAD file, 2024-03-24]
freecad/KS/Zusatzsignale/export/ZS_Zs6_Fest_NR.step
5.00 x 9.70 x 10.0 mm
