jgraichen/railway-signals/freecad/KS/Masten/export/Mast_Auslegerkorb_40.stl

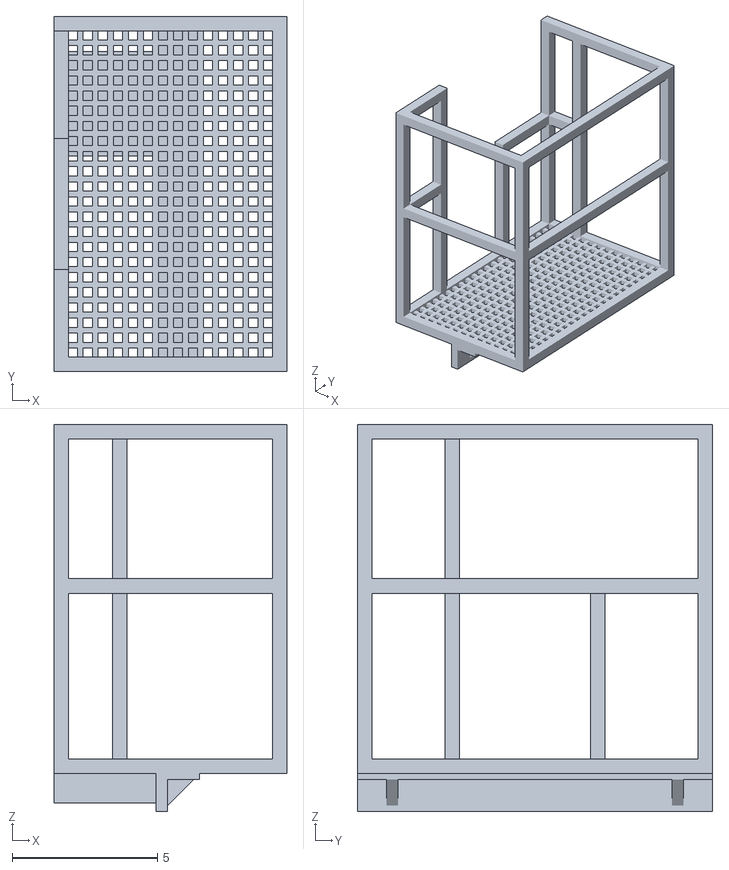
[picture p181: CAD file, 2024-03-24]
freecad/KS/Masten/export/Mast_Auslegerkorb_40.stl
8.00 x 12.2 x 13.3
