jgraichen/railway-signals/freecad/KS/Masten/export/Mast_Auslegerkorb_80.stl

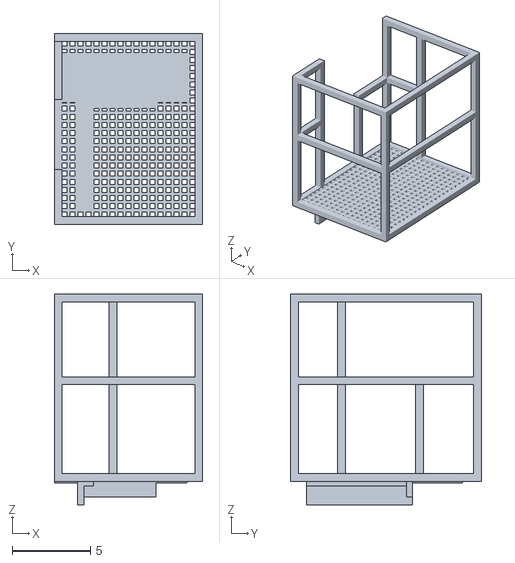
[picture p182: CAD file, 2024-03-24]
freecad/KS/Masten/export/Mast_Auslegerkorb_80.stl
9.50 x 12.2 x 13.5
