jgraichen/railway-signals/freecad/KS/Masten/export/Ausleger_Signalmast_2ZS.stl

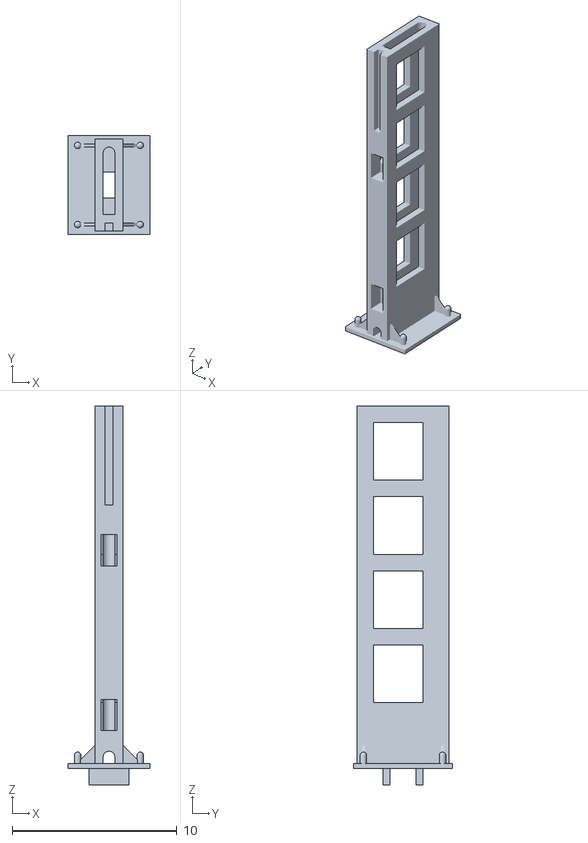
[picture p183: CAD file, 2024-01-28]
freecad/KS/Masten/export/Ausleger_Signalmast_2ZS.stl
5.00 x 6.00 x 23.0
