jgraichen/railway-signals/freecad/KS/Masten/export/Ausleger_Mast_52.stl

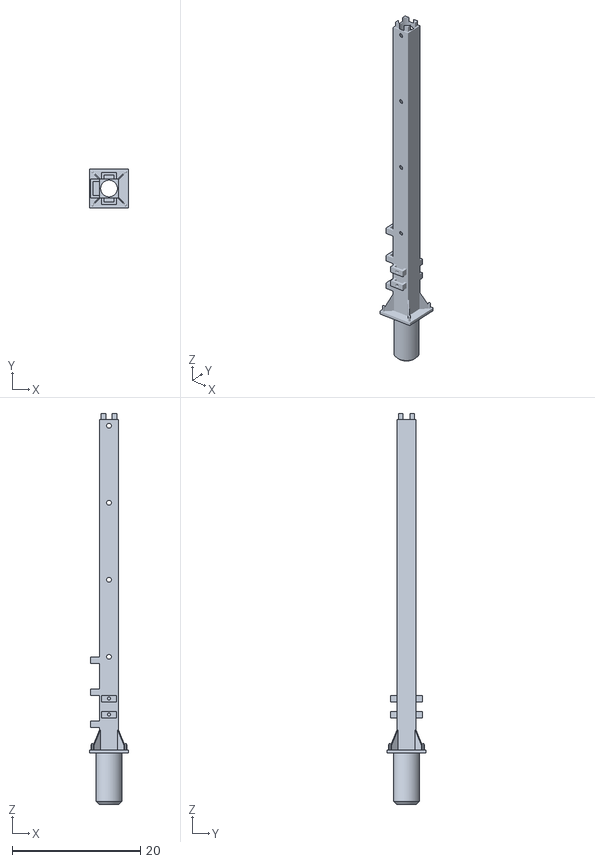
[picture p184: CAD file, 2024-01-28]
freecad/KS/Masten/export/Ausleger_Mast_52.stl
6.00 x 6.00 x 60.9
