jgraichen/railway-signals/freecad/KS/Masten/export/Auslegermast_38_40.stl

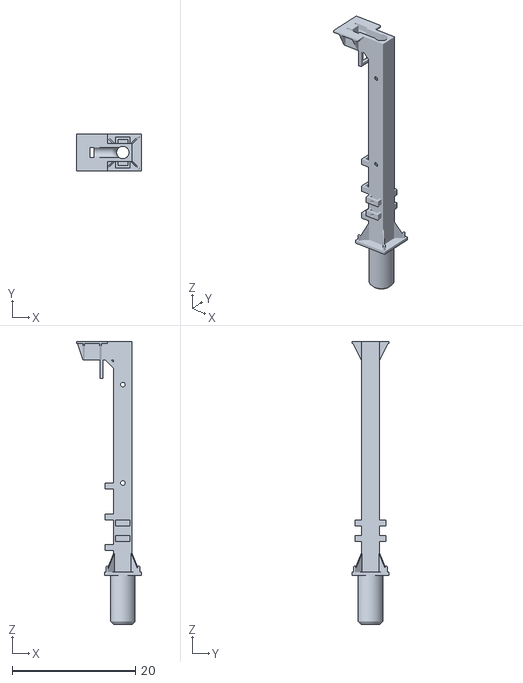
[picture p185: CAD file, 2024-01-28]
freecad/KS/Masten/export/Auslegermast_38_40.stl
10.5 x 6.00 x 46.0
