jgraichen/railway-signals/freecad/KS/Masten/export/Auslegermast_48_60.stl

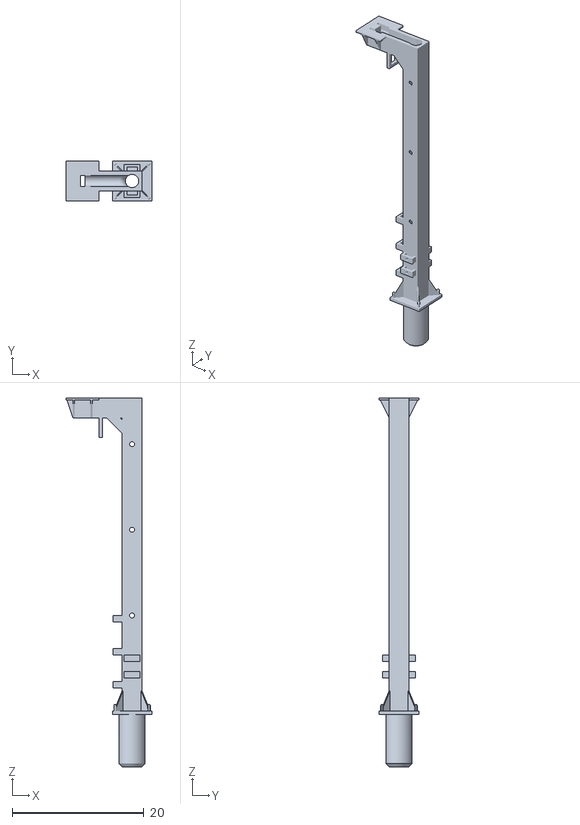
[picture p186: CAD file, 2024-01-28]
freecad/KS/Masten/export/Auslegermast_48_60.stl
13.0 x 6.00 x 56.0
