jgraichen/railway-signals/freecad/KS/Masten/export/Ausleger_Mast_32.stl

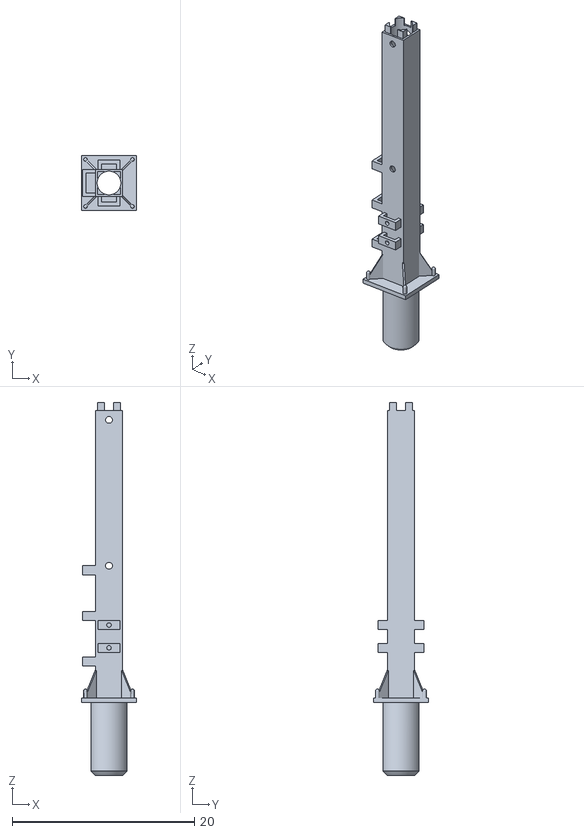
[picture p187: CAD file, 2024-01-28]
freecad/KS/Masten/export/Ausleger_Mast_32.stl
6.00 x 6.00 x 40.9
