jgraichen/railway-signals/freecad/KS/Masten/export/Auslegermast_38_80.stl

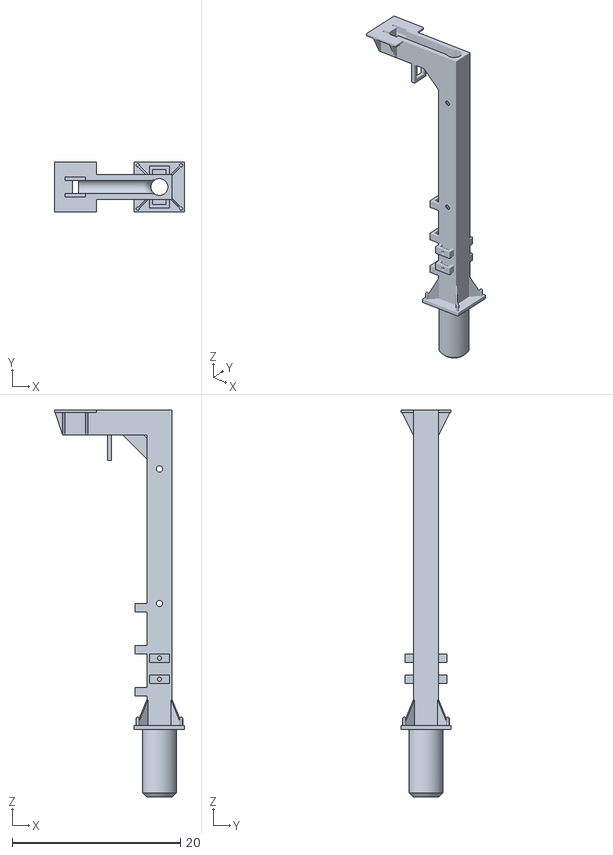
[picture p188: CAD file, 2024-01-28]
freecad/KS/Masten/export/Auslegermast_38_80.stl
15.5 x 6.00 x 46.0
