jgraichen/railway-signals/freecad/KS/Masten/export/Auslegermast_48_80.stl

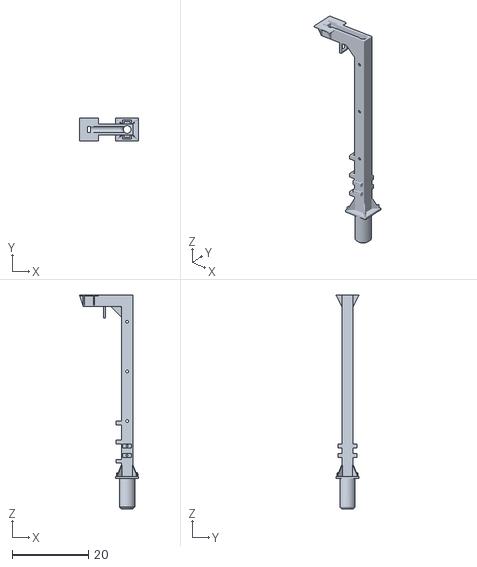
[picture p189: CAD file, 2024-01-28]
freecad/KS/Masten/export/Auslegermast_48_80.stl
15.5 x 6.00 x 56.0
