jgraichen/railway-signals/freecad/KS/Masten/export/Auslegermast_48_40.stl

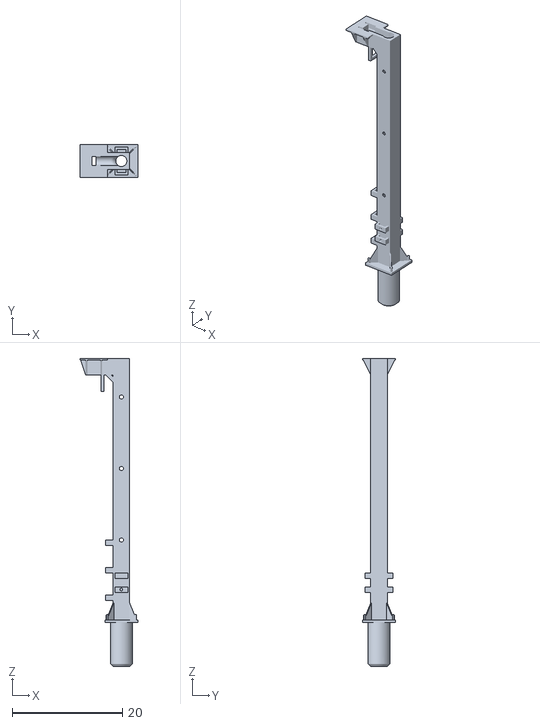
[picture p190: CAD file, 2024-01-28]
freecad/KS/Masten/export/Auslegermast_48_40.stl
10.5 x 6.00 x 56.0
