jgraichen/railway-signals/freecad/KS/Masten/export/Auslegermast_38_60.stl

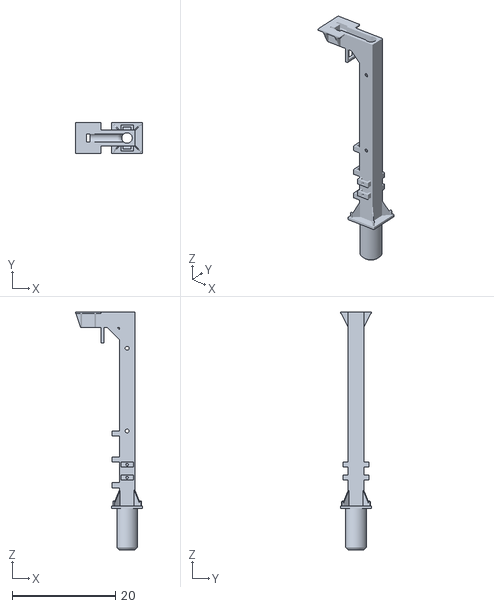
[picture p191: CAD file, 2024-01-28]
freecad/KS/Masten/export/Auslegermast_38_60.stl
13.0 x 6.00 x 46.0
