jgraichen/railway-signals/freecad/KS/Masten/export/Ausleger_Mast_42.stl

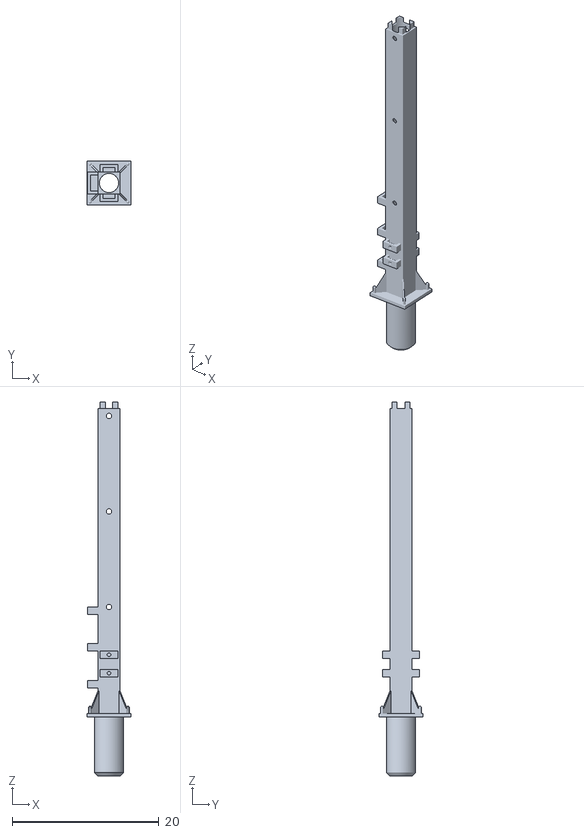
[picture p192: CAD file, 2024-01-28]
freecad/KS/Masten/export/Ausleger_Mast_42.stl
6.00 x 6.00 x 50.9
