jgraichen/railway-signals/freecad/KS/Masten/export/Ausleger_Signalmast_1ZS.stl

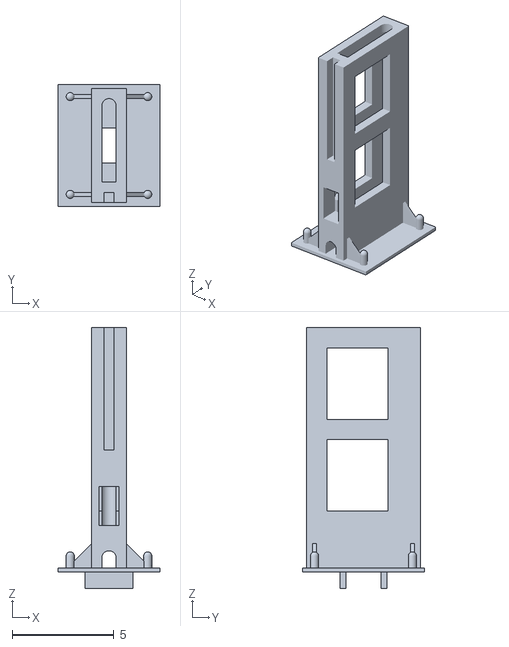
[picture p193: CAD file, 2024-01-28]
freecad/KS/Masten/export/Ausleger_Signalmast_1ZS.stl
5.00 x 6.00 x 12.8
